glydrfreak/vSpeed-Vario/Documentation/TrackWheel.JPG

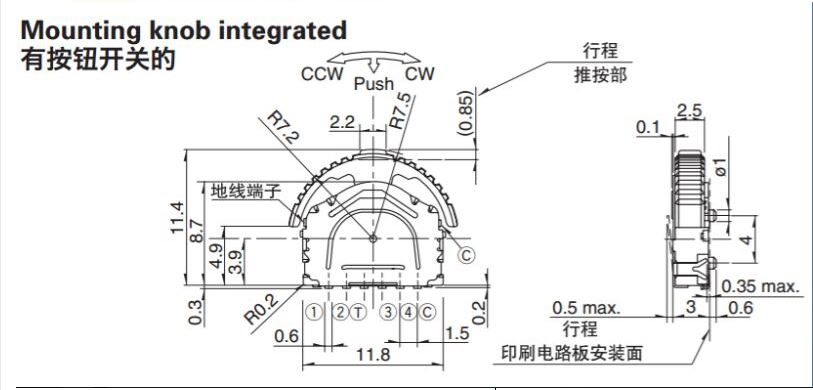
Documentation/TrackWheel.JPG
