glydrfreak/vSpeed-Vario/Documentation/vSpeed-mini-eBay/IMG-5799.JPG

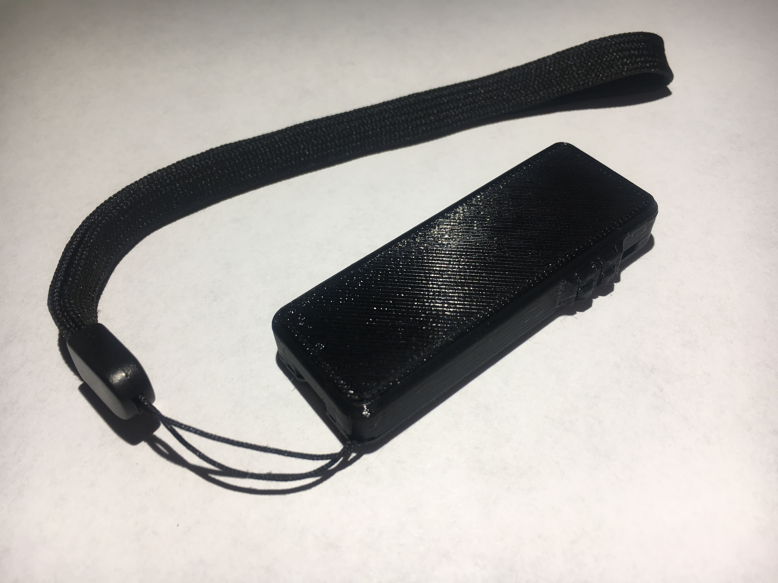
Documentation/vSpeed-mini-eBay/IMG-5799.JPG
