glydrfreak/vSpeed-Vario/Documentation/vSpeed-mini-eBay/IMG-5800.JPG

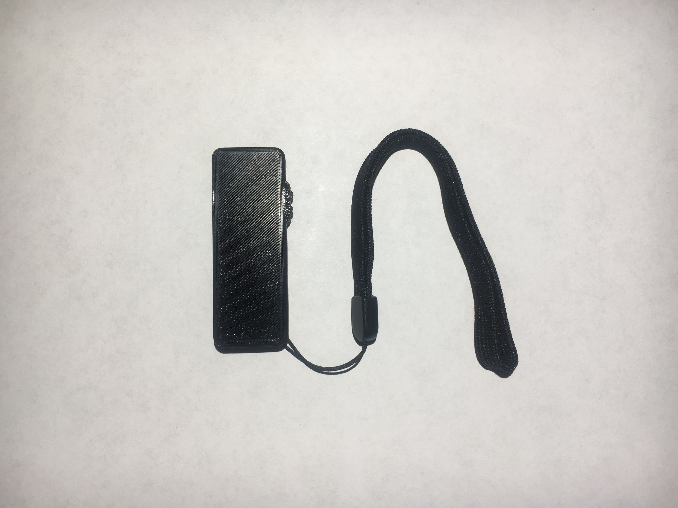
Documentation/vSpeed-mini-eBay/IMG-5800.JPG
