glydrfreak/vSpeed-Vario/Documentation/vSpeed-mini-eBay/IMG-5801.JPG

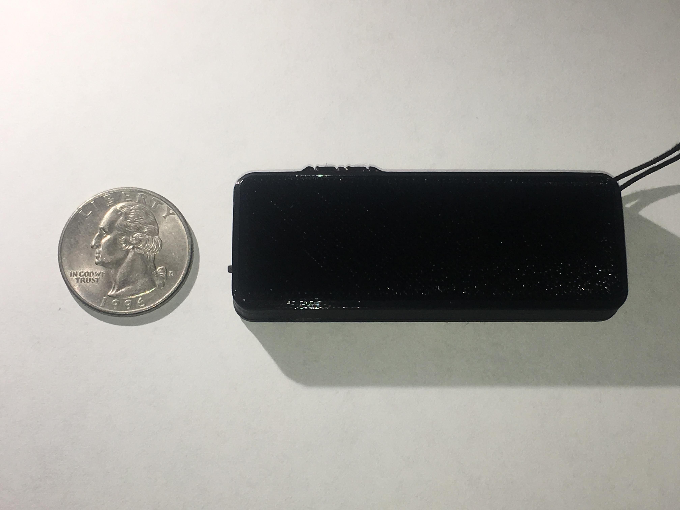
Documentation/vSpeed-mini-eBay/IMG-5801.JPG
