glydrfreak/vSpeed-Vario/Documentation/vSpeed-mini-eBay/IMG-5803.JPG

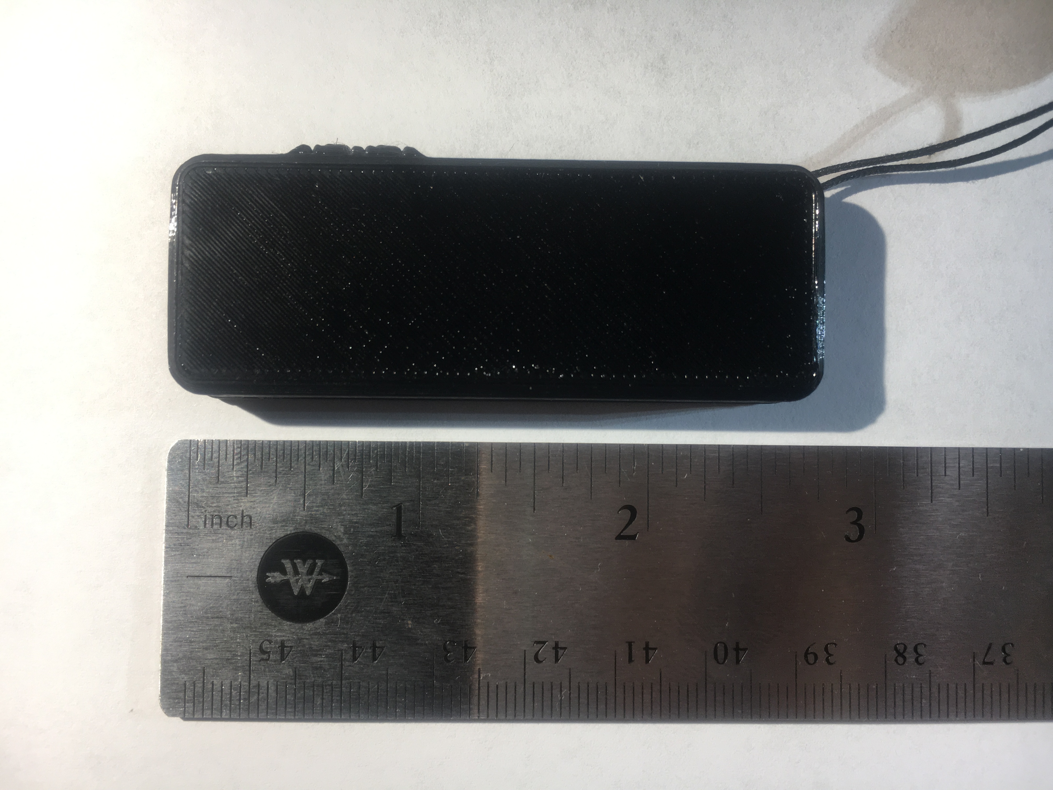
Documentation/vSpeed-mini-eBay/IMG-5803.JPG
