glydrfreak/vSpeed-Vario/Documentation/vSpeed-mini-eBay/IMG-5804.JPG

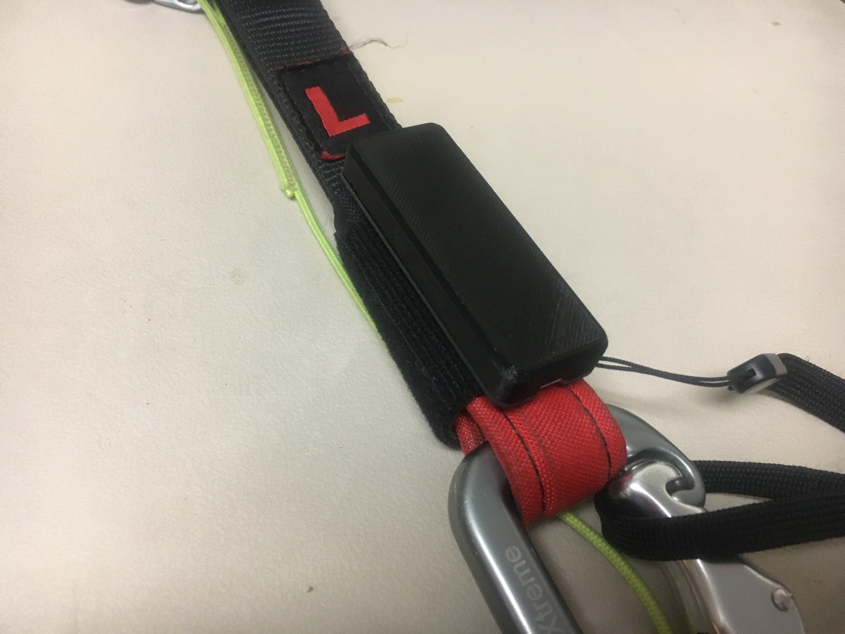
Documentation/vSpeed-mini-eBay/IMG-5804.JPG
