glydrfreak/vSpeed-Vario/Documentation/vSpeed-mini-eBay/IMG-5807.JPG

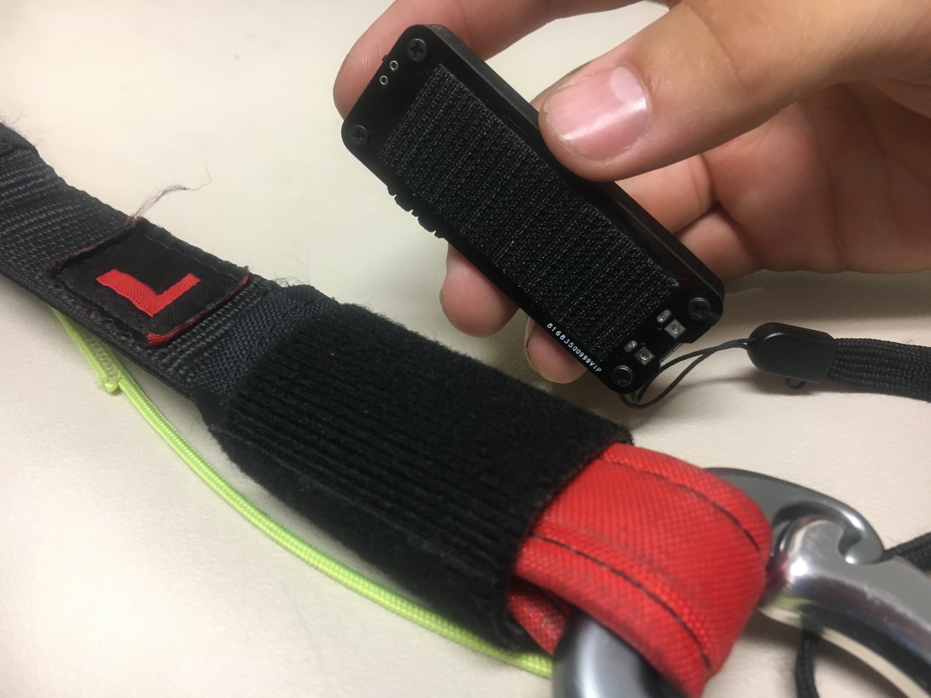
Documentation/vSpeed-mini-eBay/IMG-5807.JPG
