glydrfreak/vSpeed-Vario/Documentation/vSpeed-mini-eBay/IMG-5809.JPG

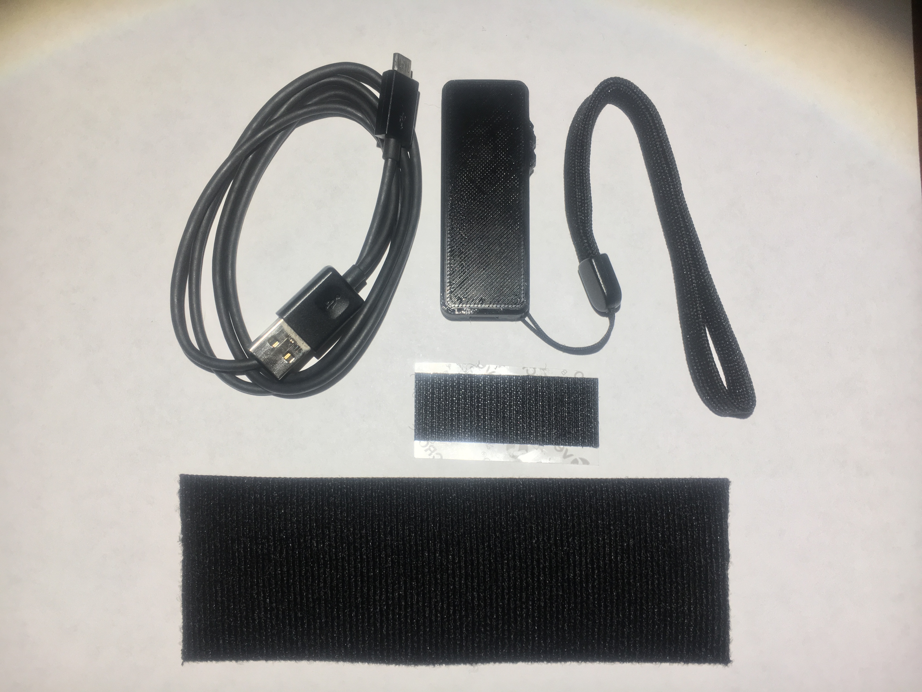
Documentation/vSpeed-mini-eBay/IMG-5809.JPG
