glydrfreak/vSpeed-Vario/Documentation/vSpeed-mini-eBay/IMG-6019.jpg

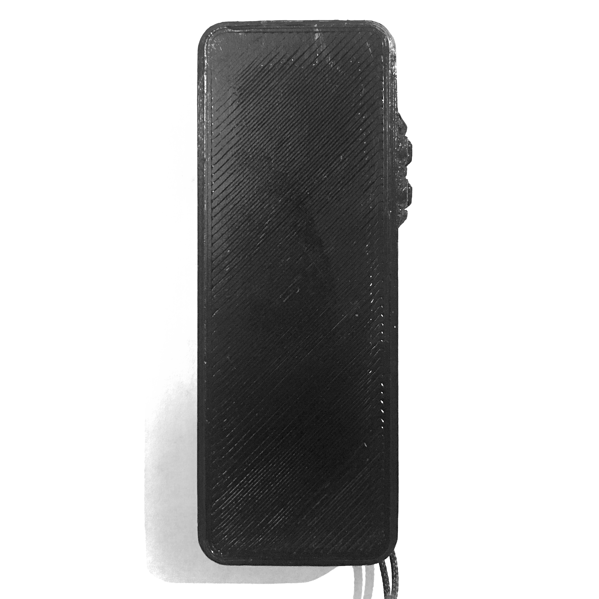
Documentation/vSpeed-mini-eBay/IMG-6019.jpg
