glydrfreak/vSpeed-Vario/Documentation/vSpeed-mini-eBay/vspeed_mini.jpg

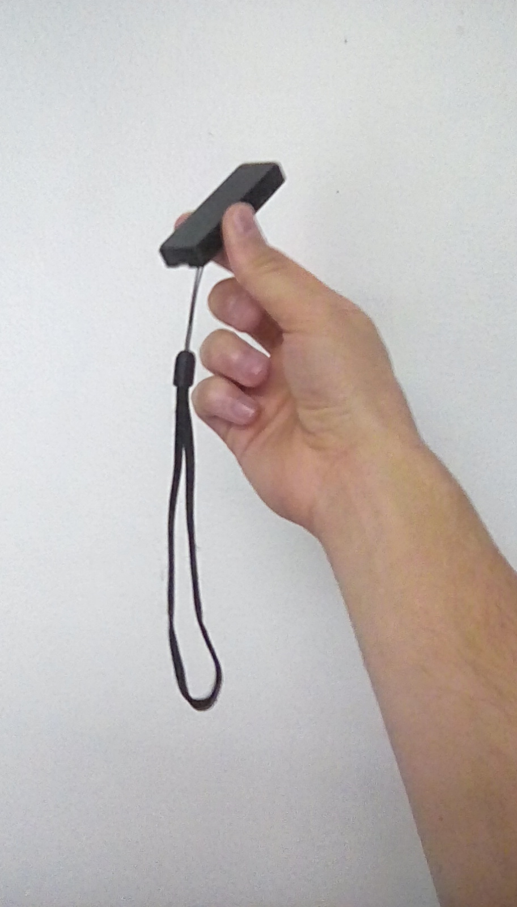
Documentation/vSpeed-mini-eBay/vspeed_mini.jpg
