glydrfreak/vSpeed-Vario/Documentation/vSpeed-mini-eBay/vSpeedMini3D - Copy.JPG

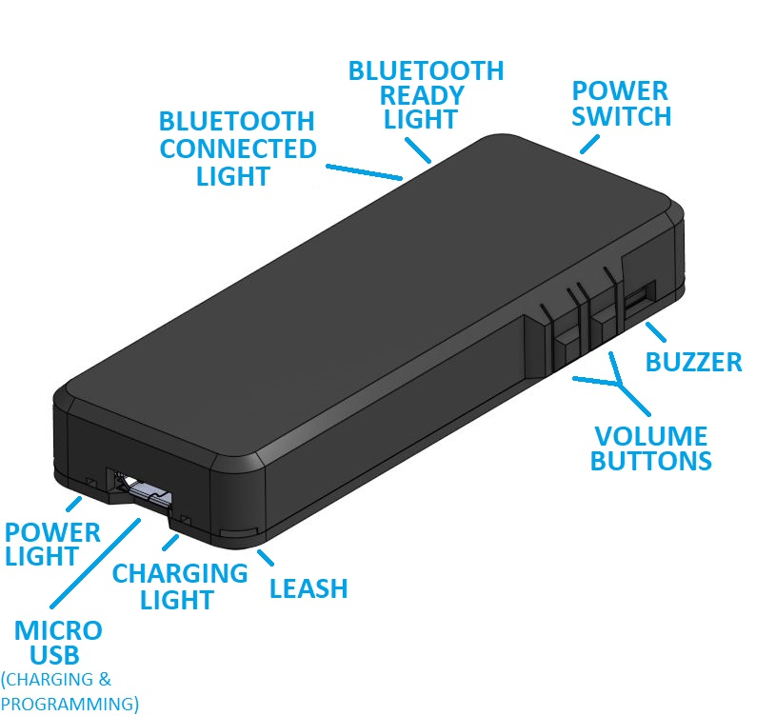
Documentation/vSpeed-mini-eBay/vSpeedMini3D - Copy.JPG
