glydrfreak/vSpeed-Vario/Images/COMPARE.JPG

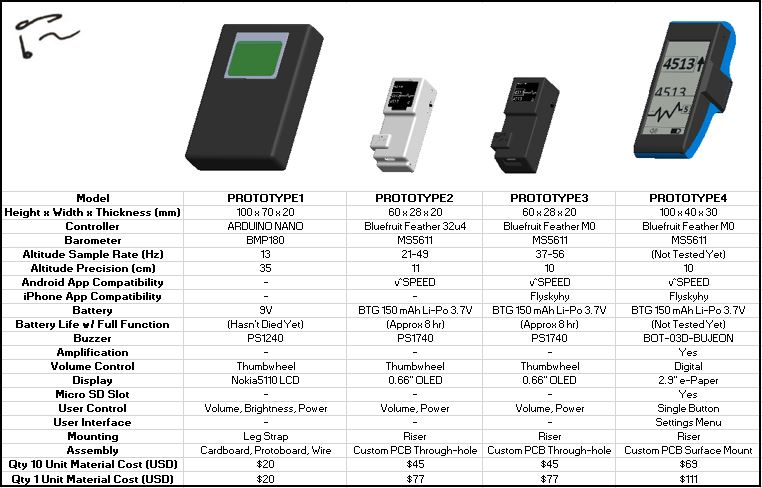
Images/COMPARE.JPG
