glydrfreak/vSpeed-Vario/Images/FAMILY.JPG

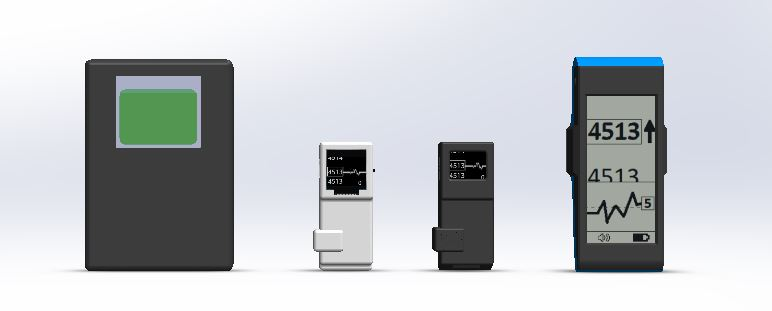
Images/FAMILY.JPG
