glydrfreak/vSpeed-Vario/Images/FAMILY_ISO.JPG

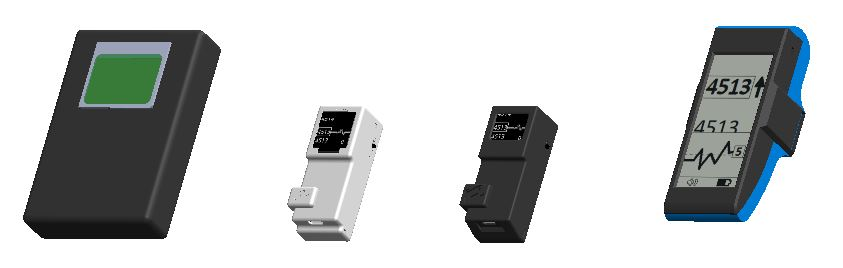
Images/FAMILY_ISO.JPG
