glydrfreak/vSpeed-Vario/Images/fsh.jpeg

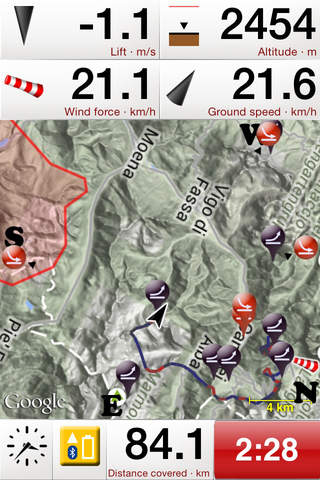
Images/fsh.jpeg
