glydrfreak/vSpeed-Vario/Images/labels.jpg

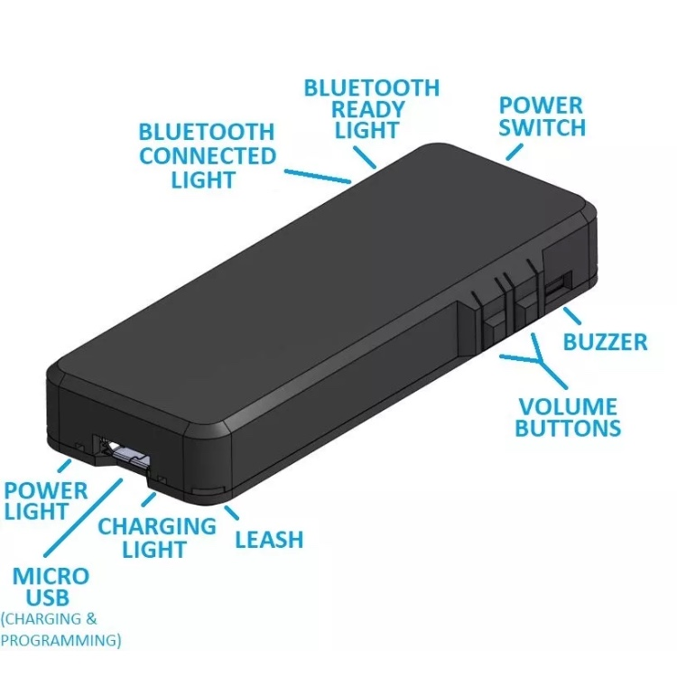
Images/labels.jpg
