glydrfreak/vSpeed-Vario/Images/NOKIA DISPLAY.png

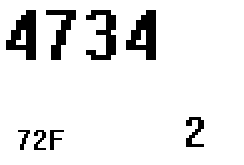
Images/NOKIA DISPLAY.png
