glydrfreak/vSpeed-Vario/Images/p4_preview.JPG

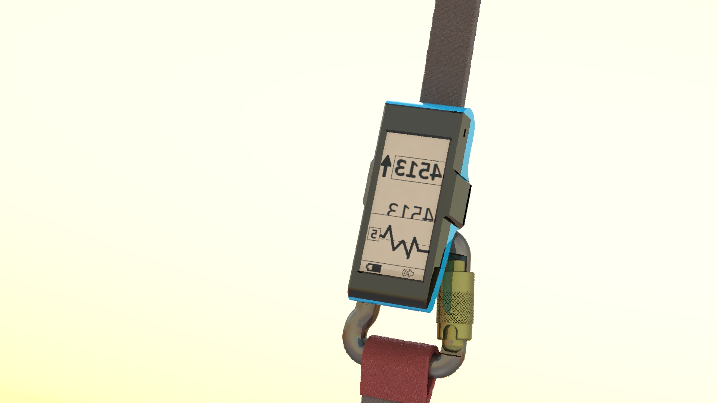
Images/p4_preview.JPG
