glydrfreak/vSpeed-Vario/Images/P5.JPG

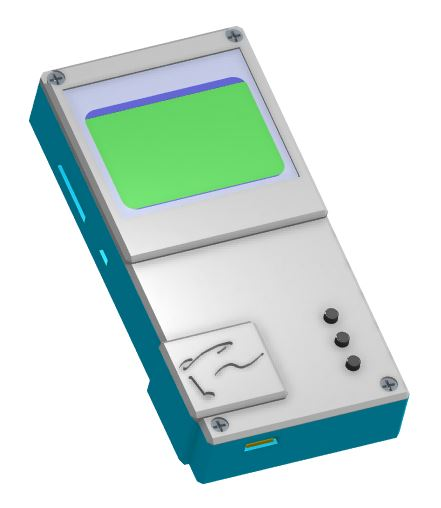
Images/P5.JPG
