glydrfreak/vSpeed-Vario/Images/P5_FOOTPRINT.JPG

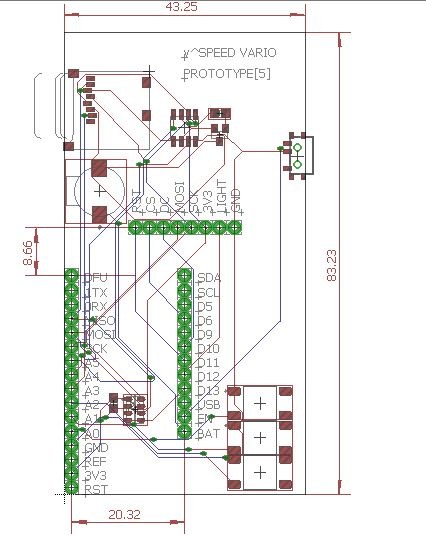
Images/P5_FOOTPRINT.JPG
