glydrfreak/vSpeed-Vario/Images/P5_PCB.JPG

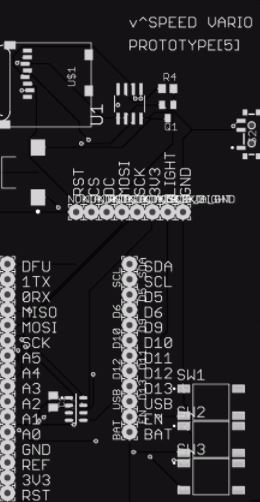
Images/P5_PCB.JPG
