glydrfreak/vSpeed-Vario/Images/P5_SIDE.JPG

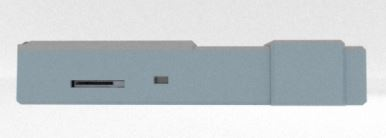
Images/P5_SIDE.JPG
