glydrfreak/vSpeed-Vario/Images/P5andP6.JPG

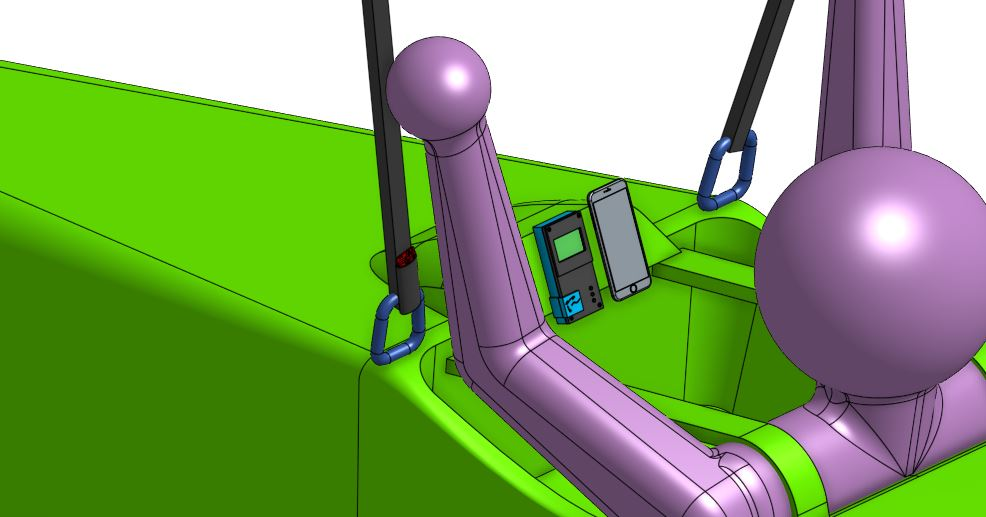
Images/P5andP6.JPG
