glydrfreak/vSpeed-Vario/Images/P6_PCB.JPG

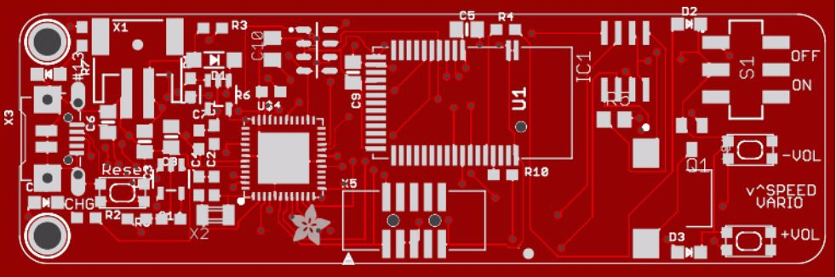
Images/P6_PCB.JPG
