glydrfreak/vSpeed-Vario/Images/P6_PCB_V2.JPG

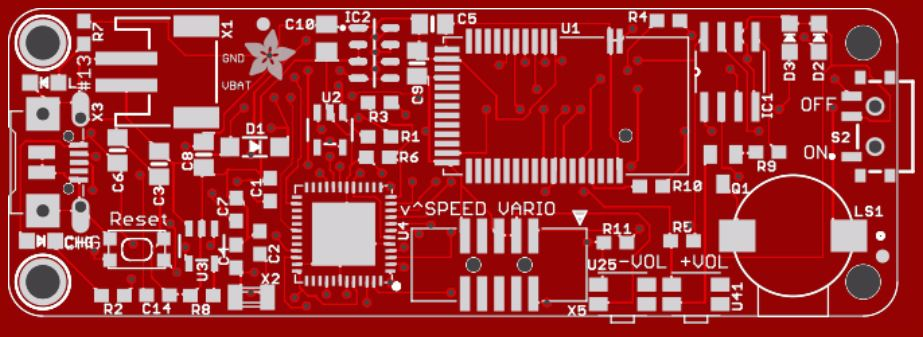
Images/P6_PCB_V2.JPG
