glydrfreak/vSpeed-Vario/Images/P6_PCB_V3.JPG

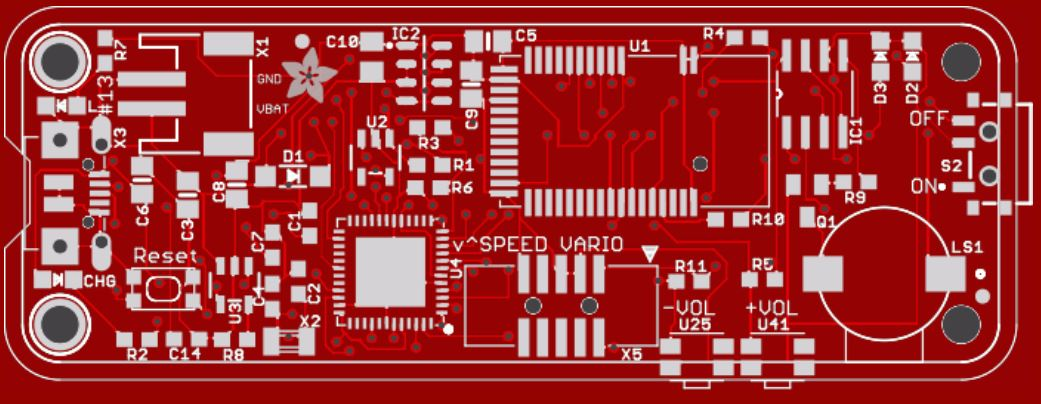
Images/P6_PCB_V3.JPG
