glydrfreak/vSpeed-Vario/Images/PROTOTYPE2.jpg

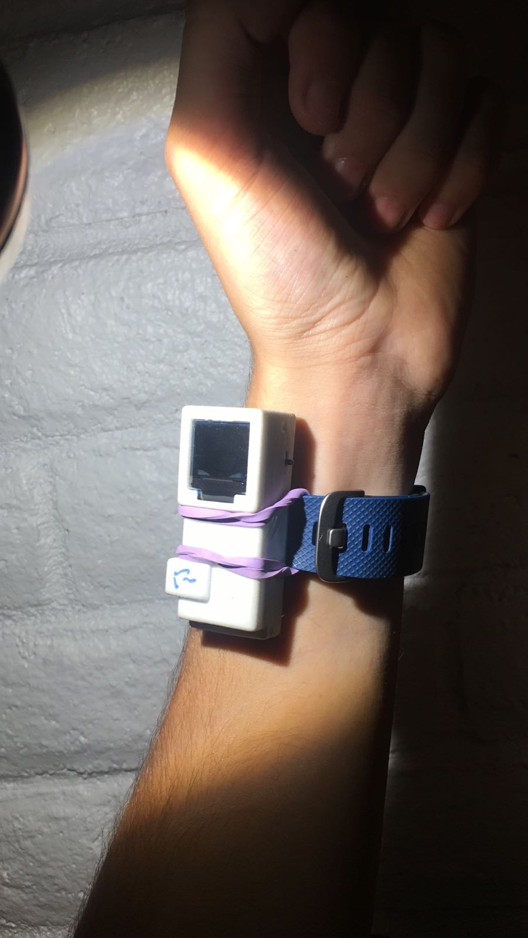
Images/PROTOTYPE2.jpg
