glydrfreak/vSpeed-Vario/Images/PROTOTYPE3AND4.JPG

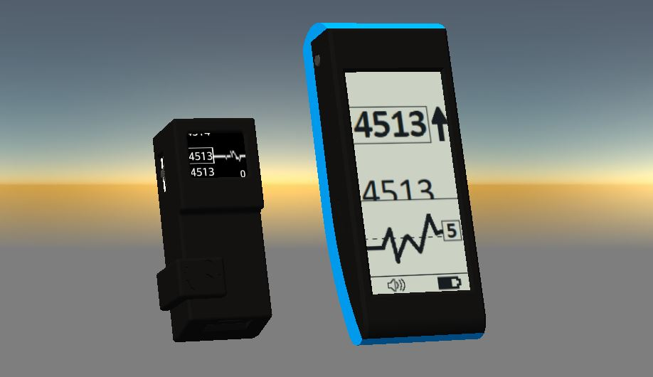
Images/PROTOTYPE3AND4.JPG
