glydrfreak/vSpeed-Vario/Images/PROTOTYPE3uncropped.jpg

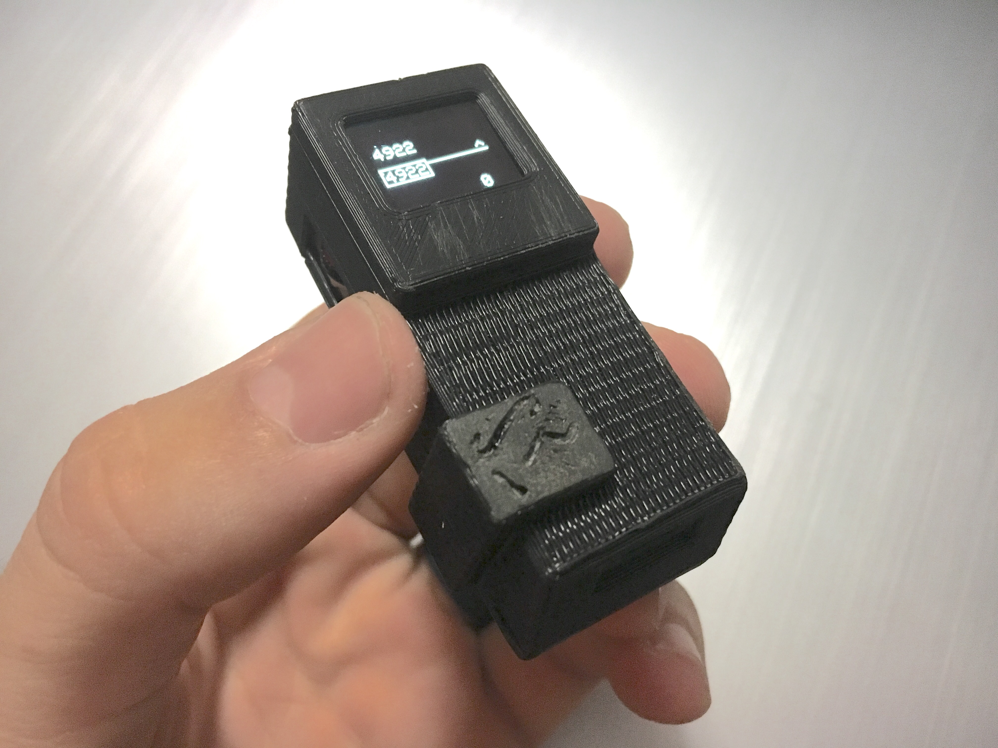
Images/PROTOTYPE3uncropped.jpg
