glydrfreak/vSpeed-Vario/Images/PROTOTYPE4.jpg

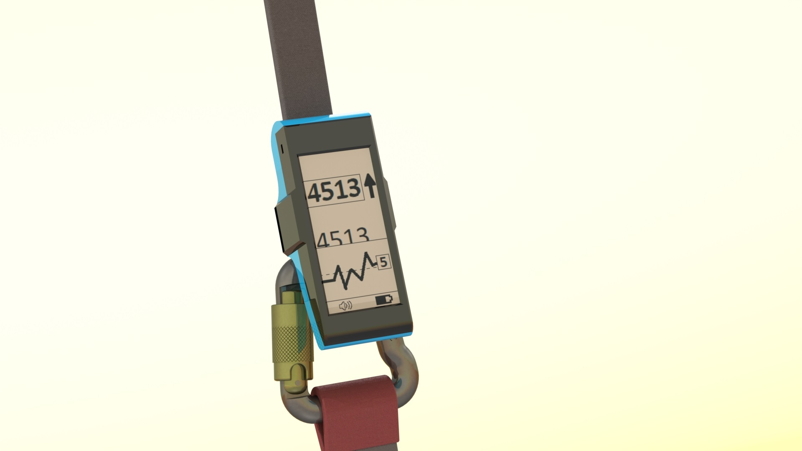
Images/PROTOTYPE4.jpg
