glydrfreak/vSpeed-Vario/Images/REFLOW_TOASTER_PCB.JPG

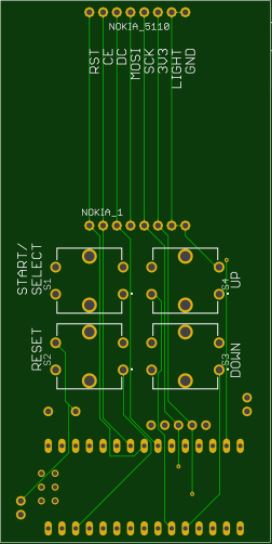
Images/REFLOW_TOASTER_PCB.JPG
