glydrfreak/vSpeed-Vario/Images/ssf3.JPG

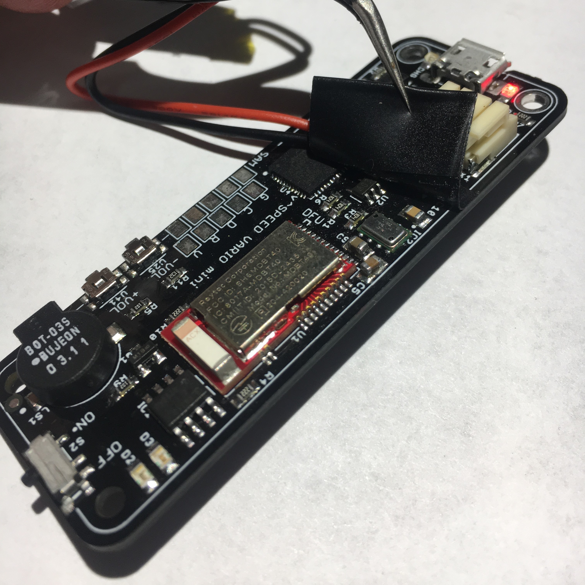
Images/ssf3.JPG
