glydrfreak/vSpeed-Vario/Images/ssf4.JPG

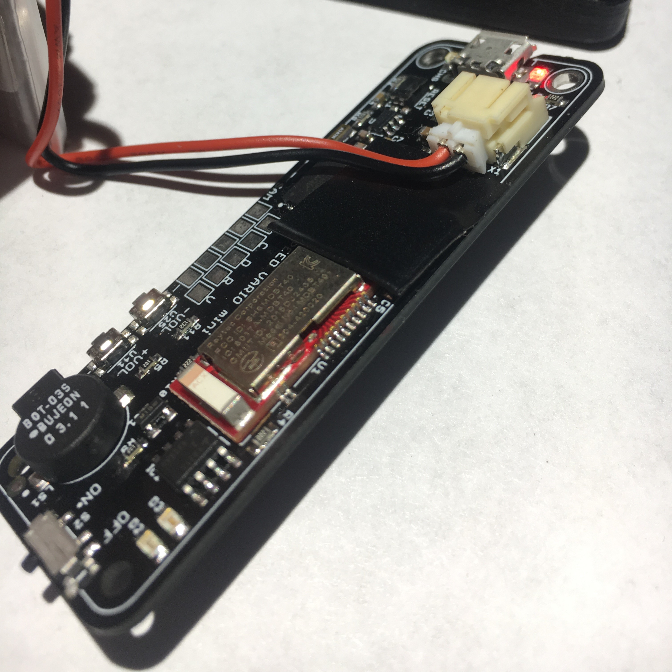
Images/ssf4.JPG
