glydrfreak/vSpeed-Vario/SolidWorks/P1.new/frente.jpg

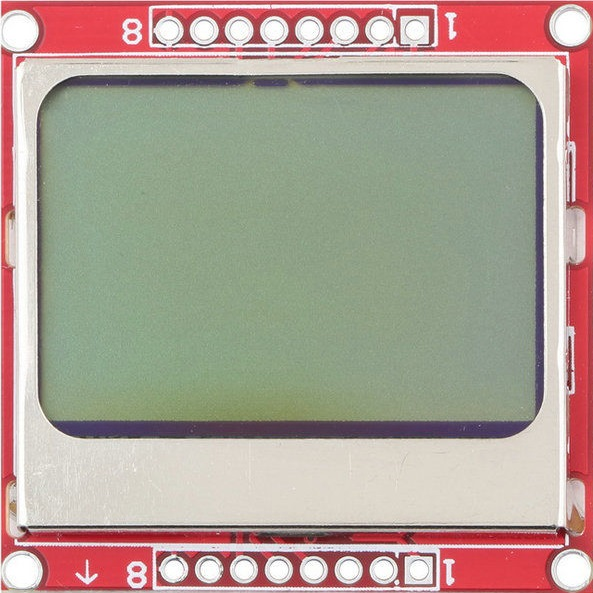
SolidWorks/P1.new/frente.jpg
