glydrfreak/vSpeed-Vario/SolidWorks/P1.new/tras.jpg

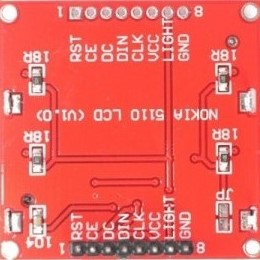
SolidWorks/P1.new/tras.jpg
