glydrfreak/vSpeed-Vario/SolidWorks/P2.new/android.jpg

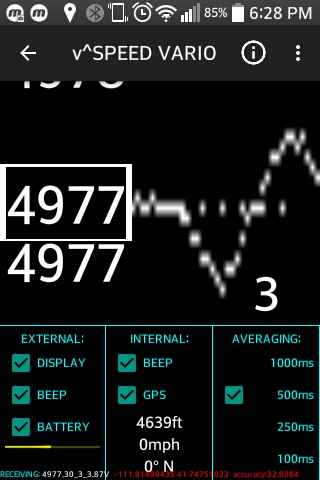
SolidWorks/P2.new/android.jpg
