glydrfreak/vSpeed-Vario/SolidWorks/P2.new/bluefruit feather 32u4 bottom.jpg

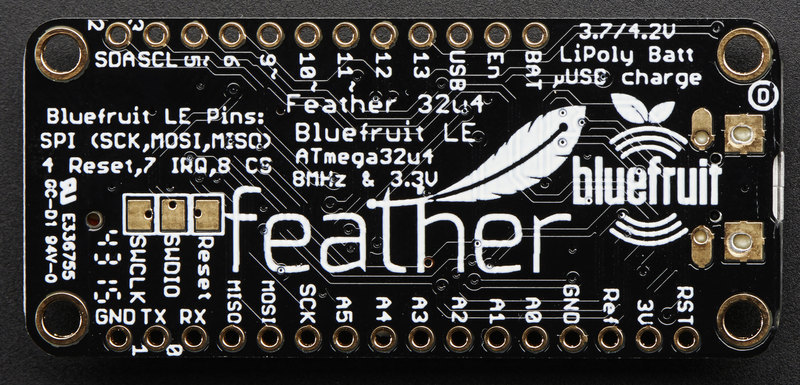
SolidWorks/P2.new/bluefruit feather 32u4 bottom.jpg
