glydrfreak/vSpeed-Vario/SolidWorks/P2.new/bluefruit feather 32u4.jpg

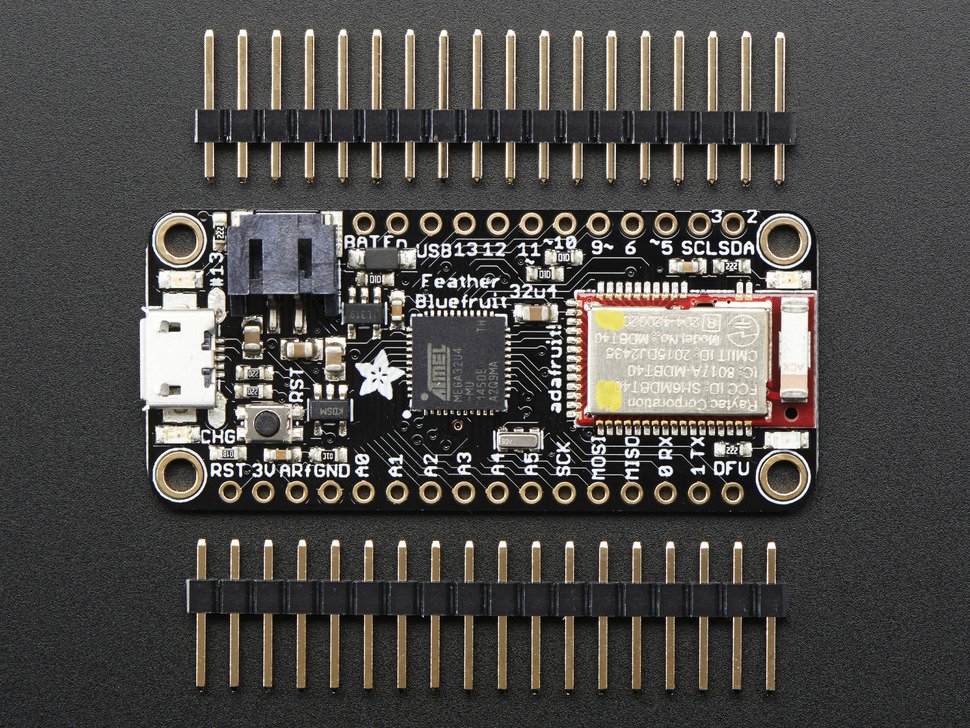
SolidWorks/P2.new/bluefruit feather 32u4.jpg
