glydrfreak/vSpeed-Vario/SolidWorks/P2.new/custom pcb 1.2.4.jpg

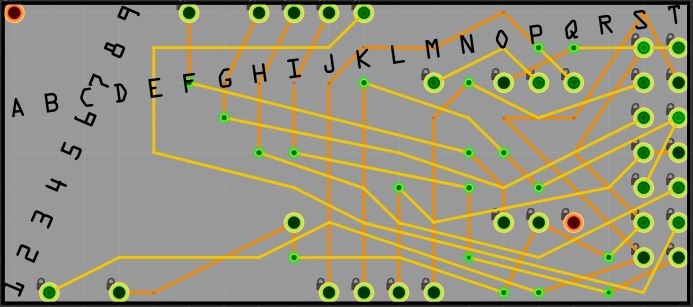
SolidWorks/P2.new/custom pcb 1.2.4.jpg
