glydrfreak/vSpeed-Vario/SolidWorks/P2.new/ms5611.jpg

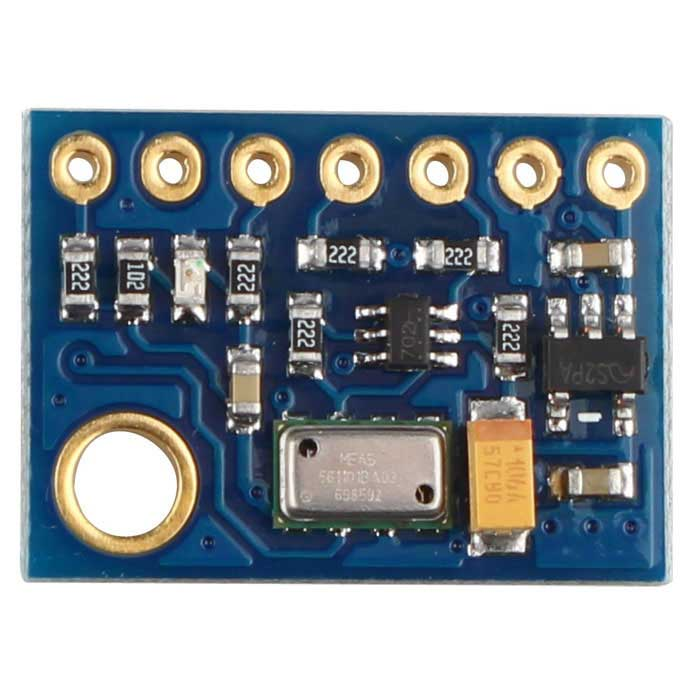
SolidWorks/P2.new/ms5611.jpg
