glydrfreak/vSpeed-Vario/SolidWorks/P2.new/s-l1600 (1).jpg

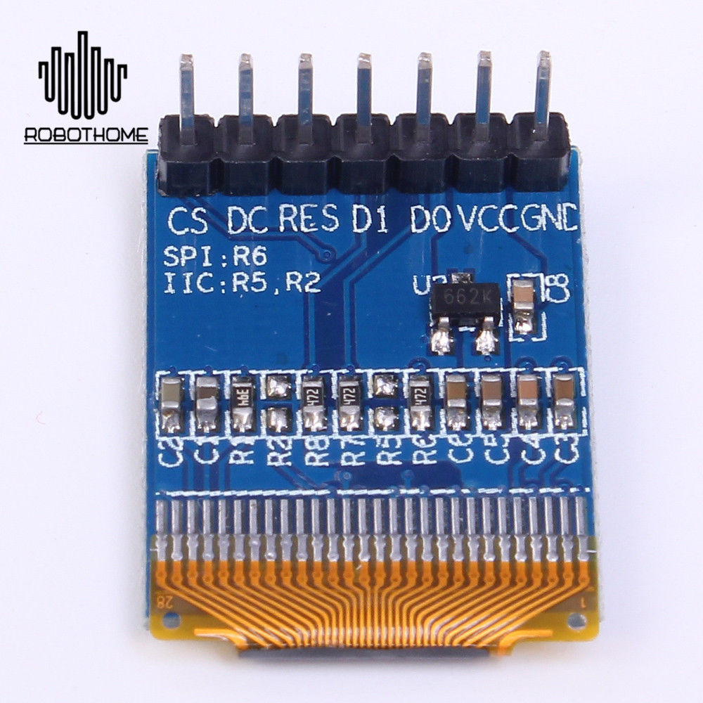
SolidWorks/P2.new/s-l1600 (1).jpg
