glydrfreak/vSpeed-Vario/SolidWorks/P4.new/bottom_pcb.jpg

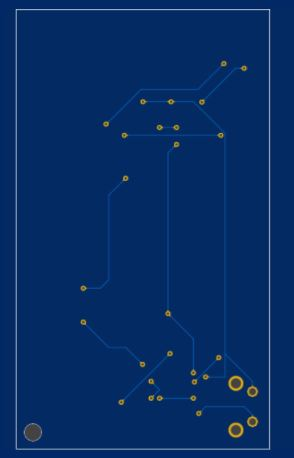
SolidWorks/P4.new/bottom_pcb.jpg
