glydrfreak/vSpeed-Vario/SolidWorks/P4.new/cotton burgundy.jpg

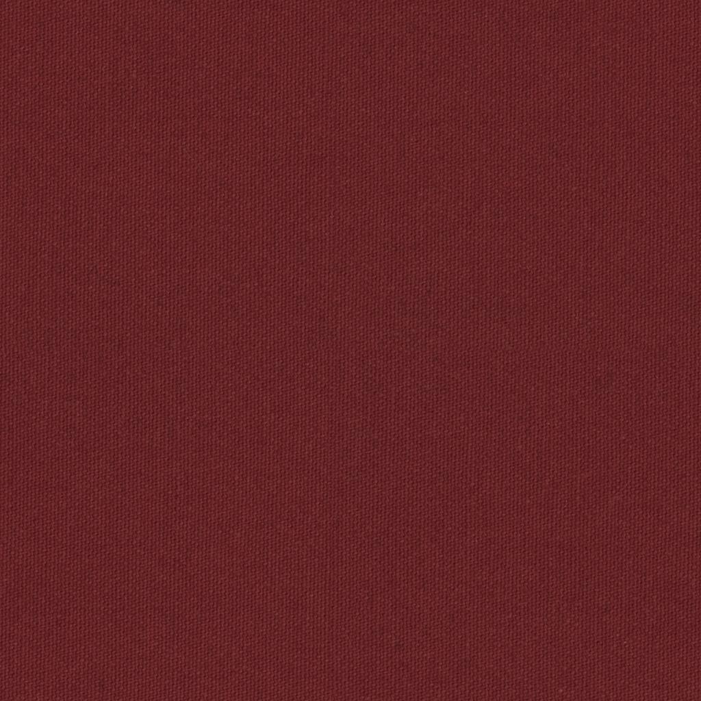
SolidWorks/P4.new/cotton burgundy.jpg
