glydrfreak/vSpeed-Vario/SolidWorks/P4.new/cotton grey.jpg

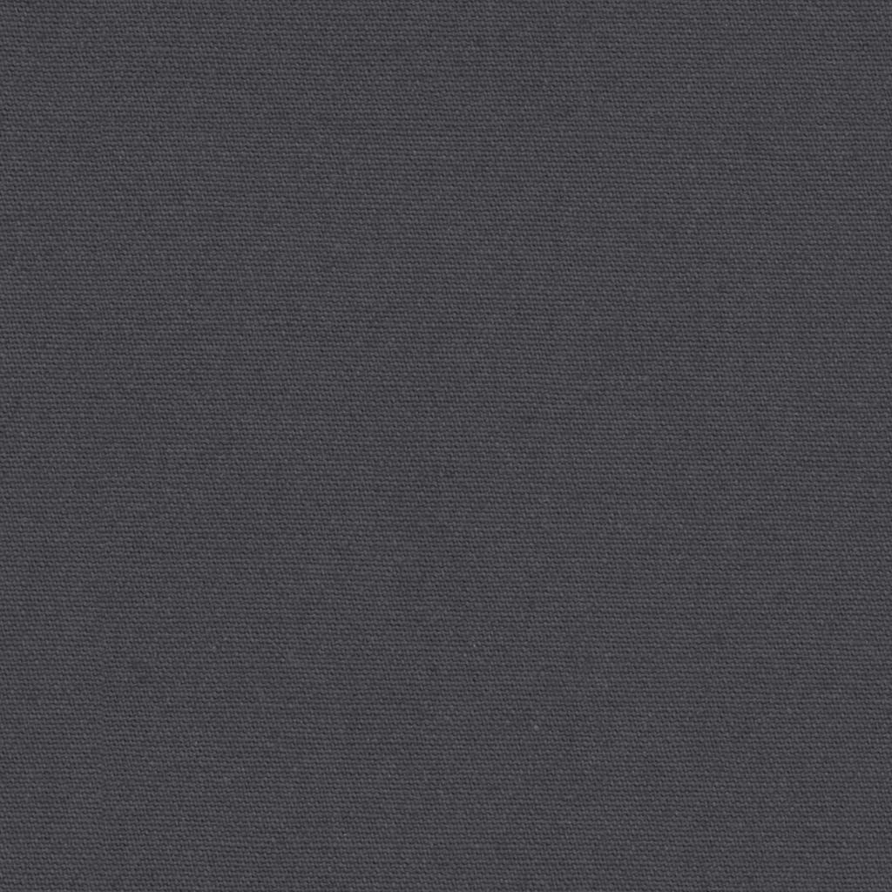
SolidWorks/P4.new/cotton grey.jpg
