glydrfreak/vSpeed-Vario/SolidWorks/P4.new/sky_environment.jpg

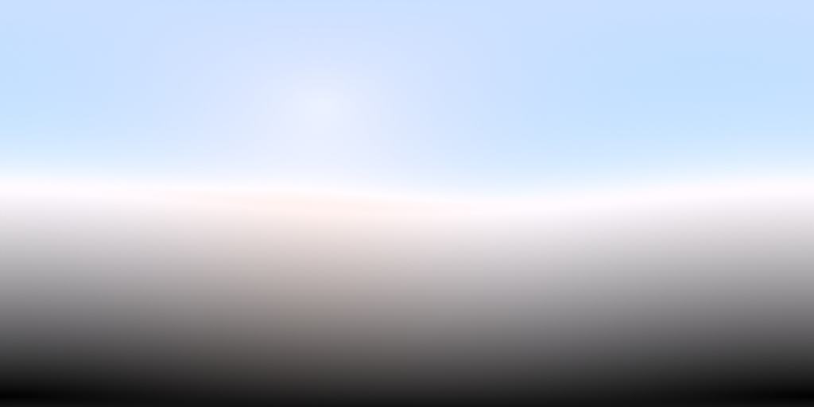
SolidWorks/P4.new/sky_environment.jpg
