glydrfreak/vSpeed-Vario/SolidWorks/P4/COMPARISON.JPG

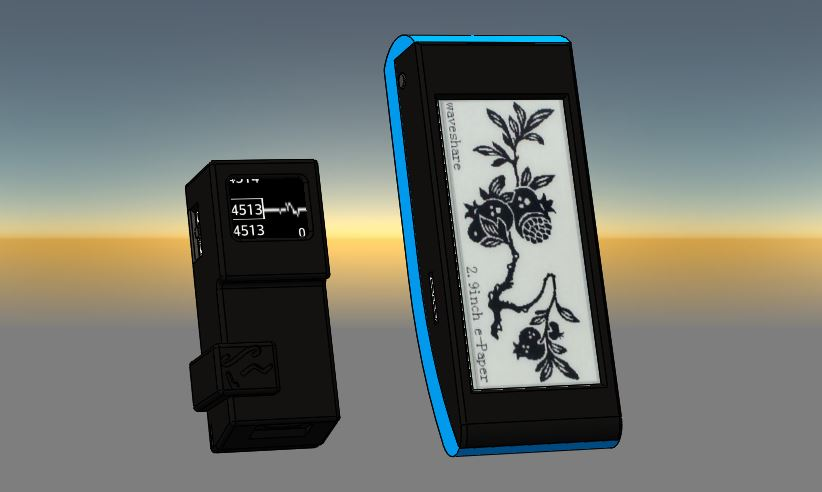
SolidWorks/P4/COMPARISON.JPG
