glydrfreak/vSpeed-Vario/SolidWorks/P4/PLACEMENT.JPG

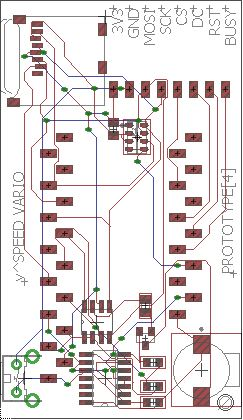
SolidWorks/P4/PLACEMENT.JPG
