glydrfreak/vSpeed-Vario/SolidWorks/P4/ROUGH ACTUAL SIZE.JPG

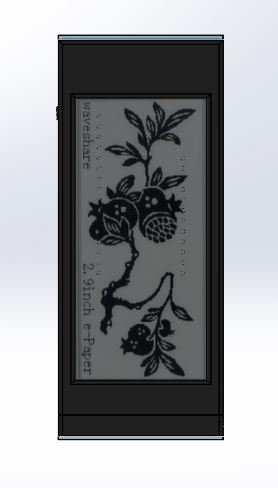
SolidWorks/P4/ROUGH ACTUAL SIZE.JPG
