glydrfreak/vSpeed-Vario/SolidWorks/P4/SCREEN_COMPARISON.JPG

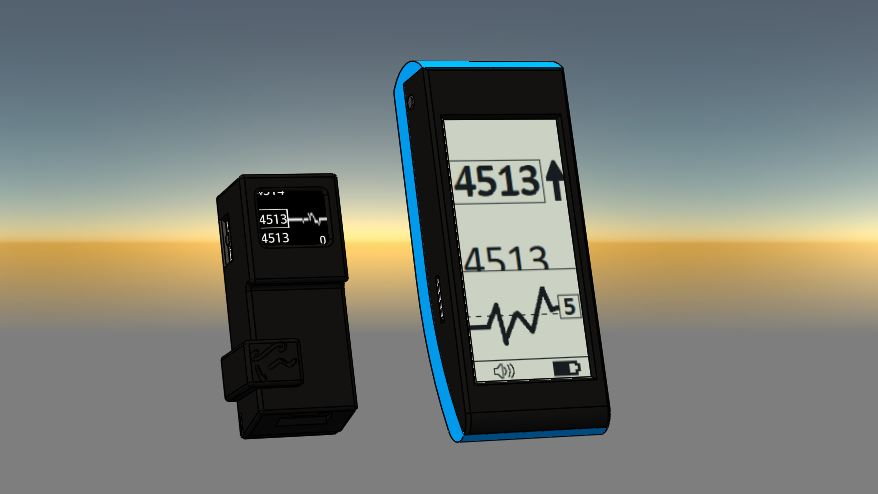
SolidWorks/P4/SCREEN_COMPARISON.JPG
