glydrfreak/vSpeed-Vario/SolidWorks/P4/stencil.JPG

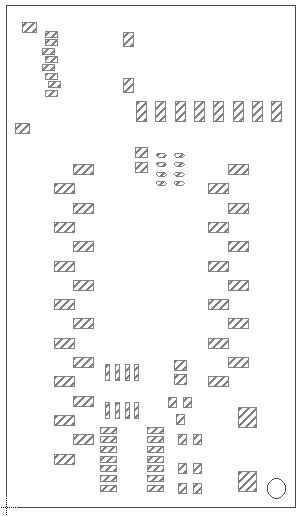
SolidWorks/P4/stencil.JPG
