glydrfreak/vSpeed-Vario/SolidWorks/P4/sunset.JPG

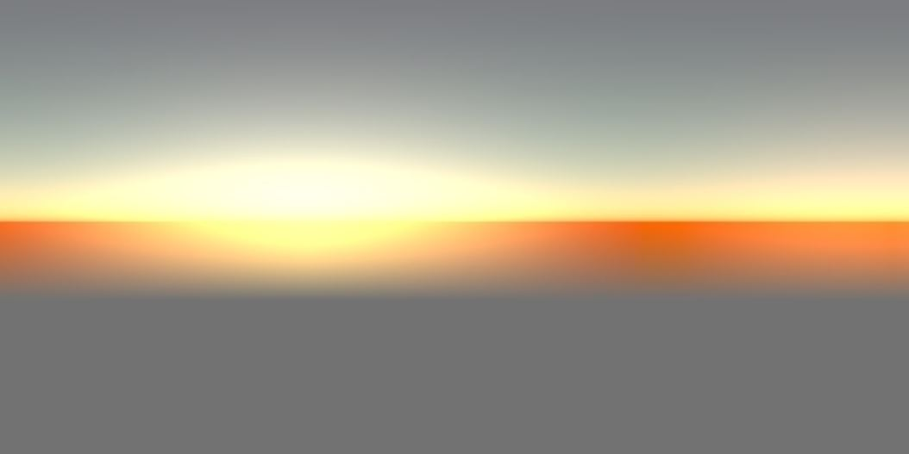
SolidWorks/P4/sunset.JPG
