glydrfreak/vSpeed-Vario/SolidWorks/P6/BOM_Template_2017_06_30.csv

Designator | Manufacturer Part Number | Quantity
C1,C2,C3,C4,C5 | RHA0J471MCN1GS | 5
A1,A4 | 318020010 | 2
D1 | CYBLE-014008-00 | 1
