glydrfreak/vSpeed-Vario/BillOfMaterials/ExplodedView.JPG

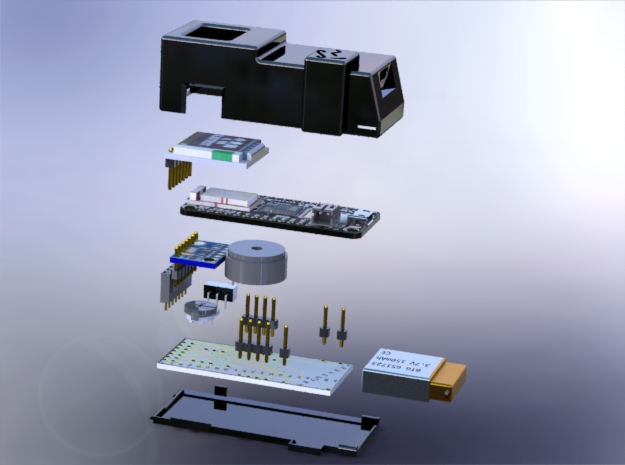
BillOfMaterials/ExplodedView.JPG
