glydrfreak/vSpeed-Vario/SolidWorks/P5/V2/CASE_FRONT V2.stl

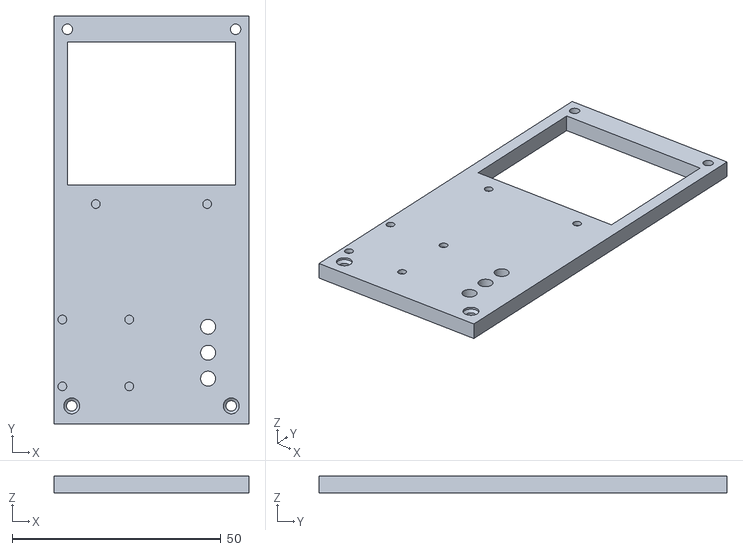
[picture p93: CAD file, 2018-03-19]
SolidWorks/P5/V2/CASE_FRONT V2.stl
46.7 x 97.6 x 4.00
