glydrfreak/vSpeed-Vario/SolidWorks/P6/3220-10-0300/3220-10-0300.igs

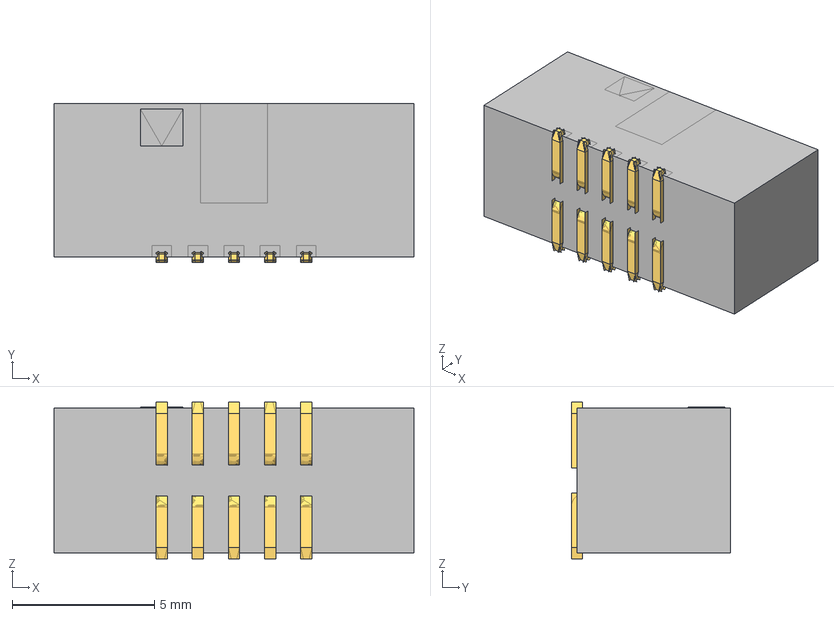
[picture p94: CAD file, 2018-04-02]
SolidWorks/P6/3220-10-0300/3220-10-0300.igs
12.7 x 5.60 x 5.50 mm
