glydrfreak/vSpeed-Vario/SolidWorks/P6/P6_CASE.stl

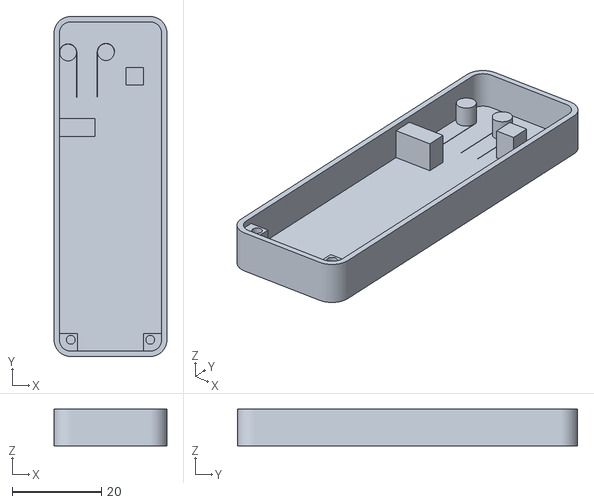
[picture p95: CAD file, 2018-04-02]
SolidWorks/P6/P6_CASE.stl
25.3 x 76.1 x 8.20
