glydrfreak/vSpeed-Vario/SolidWorks/P1.new/placa.SLDPRT

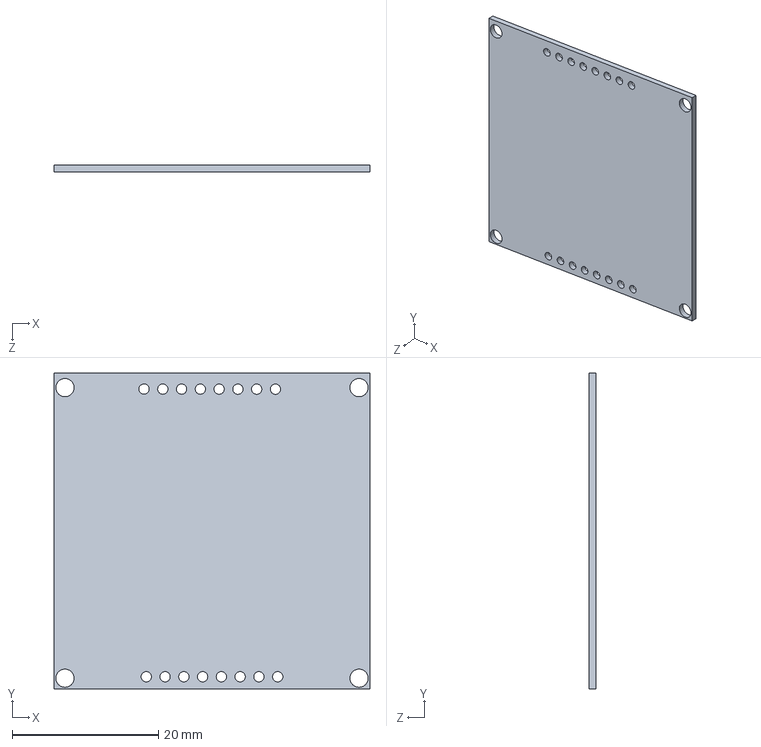
[picture p96: CAD file, 2017-11-29]
SolidWorks/P1.new/placa.SLDPRT
43.2 x 43.2 x 1.00 mm
