glydrfreak/vSpeed-Vario/SolidWorks/P2.new/POT THUMBWHEEL HORIZONTAL.SLDPRT

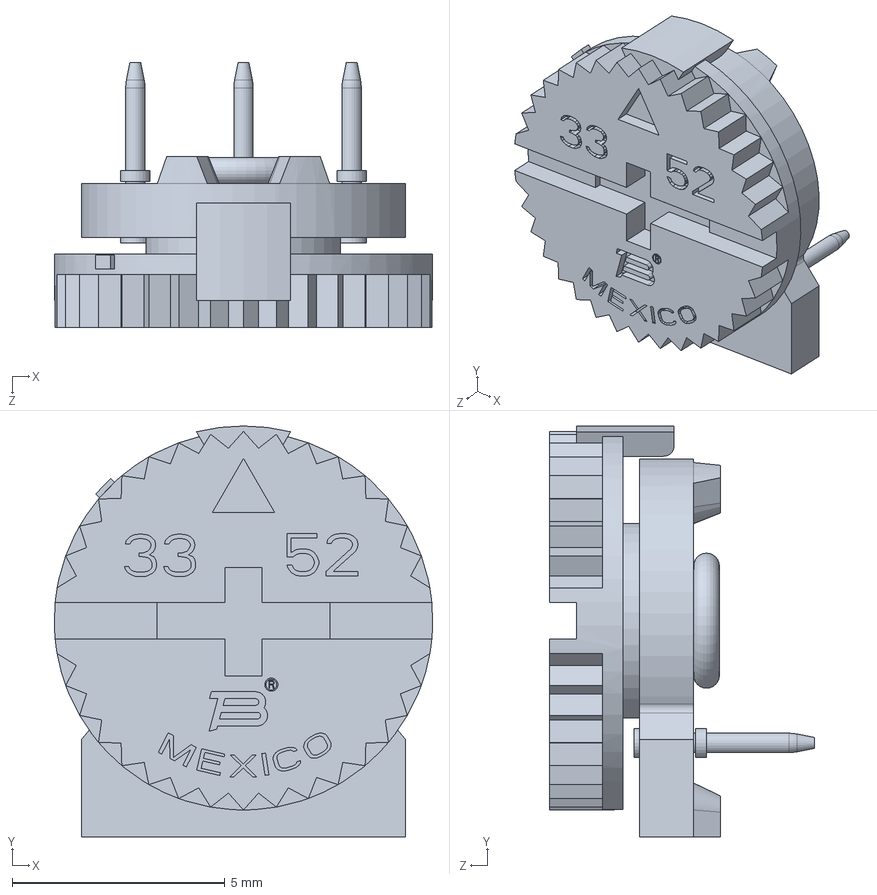
[picture p97: CAD file, 2017-11-29]
SolidWorks/P2.new/POT THUMBWHEEL HORIZONTAL.SLDPRT
8.89 x 9.65 x 6.22 mm
