glydrfreak/vSpeed-Vario/SolidWorks/P4.new/P4_BLUEFRUIT FEATHER.SLDPRT

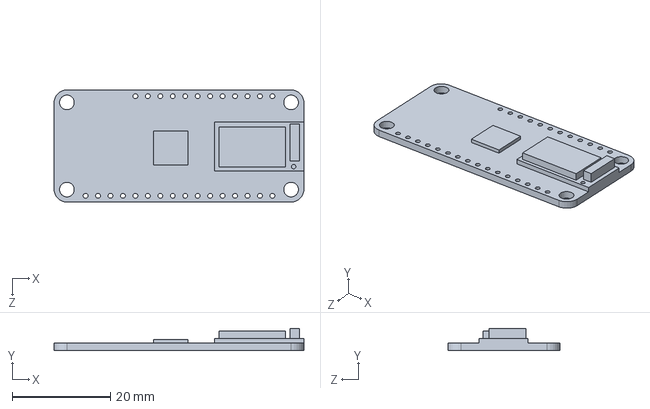
[picture p98: CAD file, 2018-03-09]
SolidWorks/P4.new/P4_BLUEFRUIT FEATHER.SLDPRT
51.0 x 4.50 x 22.9 mm
