glydrfreak/vSpeed-Vario/SolidWorks/P4/P4_JST XH 8 S8B-XH-A1 shrouded header connector v4.SLDPRT

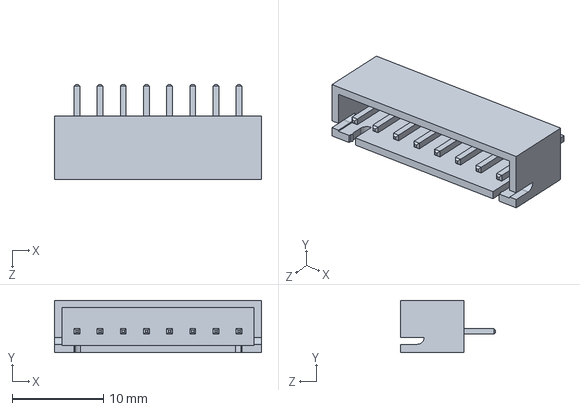
[picture p99: CAD file, 2017-12-11]
SolidWorks/P4/P4_JST XH 8 S8B-XH-A1 shrouded header connector v4.SLDPRT
22.7 x 5.75 x 10.4 mm
