glydrfreak/vSpeed-Vario/SolidWorks/P5/V2/CASE_CORNER V2.stl

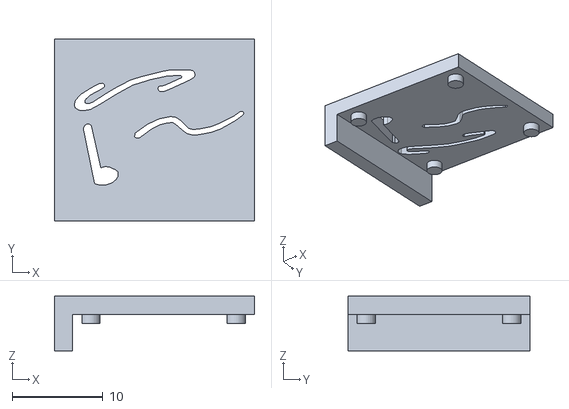
[picture p100: CAD file, 2018-03-19]
SolidWorks/P5/V2/CASE_CORNER V2.stl
22.0 x 20.0 x 6.00
