glydrfreak/vSpeed-Vario/SolidWorks/P6/XZxx54-1.sldprt

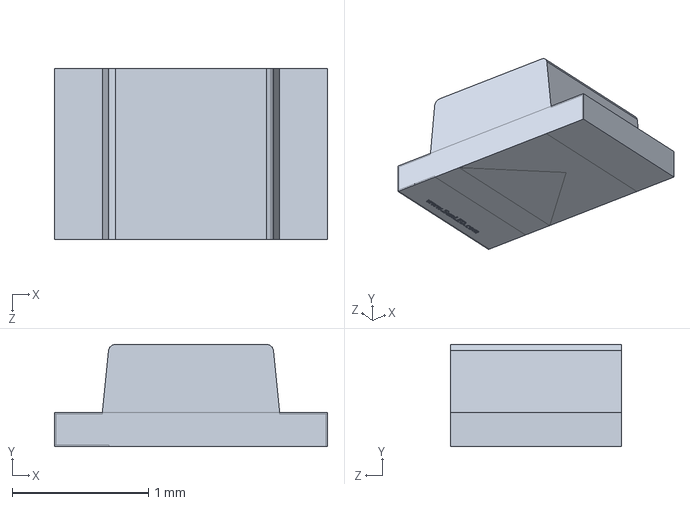
[picture p101: CAD file, 2018-04-02]
SolidWorks/P6/XZxx54-1.sldprt
2.00 x 0.75 x 1.25 mm
