glydrfreak/vSpeed-Vario/SolidWorks/P2.new/P2 CASE - FRONT SHELL.SLDPRT

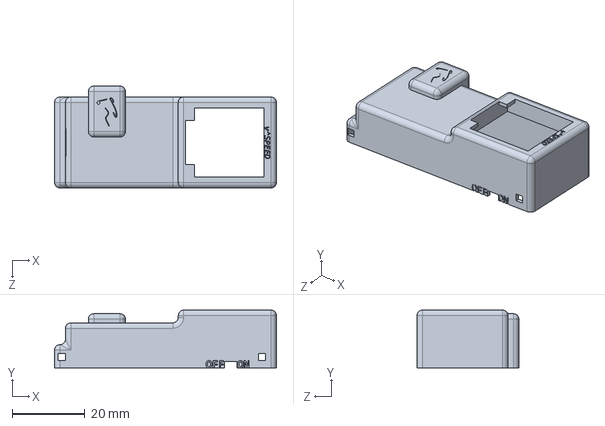
[picture p102: CAD file, 2017-11-29]
SolidWorks/P2.new/P2 CASE - FRONT SHELL.SLDPRT
61.0 x 15.9 x 28.0 mm
