glydrfreak/vSpeed-Vario/SolidWorks/P3.new/p3_PS1740.SLDPRT

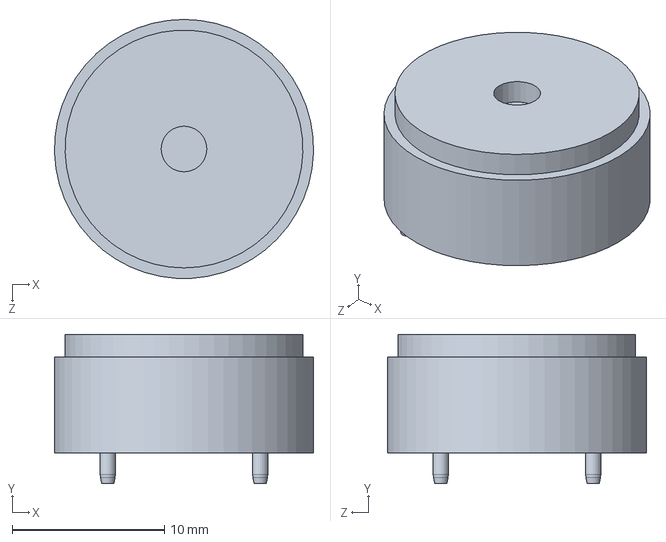
[picture p103: CAD file, 2017-11-29]
SolidWorks/P3.new/p3_PS1740.SLDPRT
17.0 x 9.80 x 17.0 mm
