glydrfreak/vSpeed-Vario/SolidWorks/P4/P4_PCB_FOR_2.9_EPD.SLDPRT

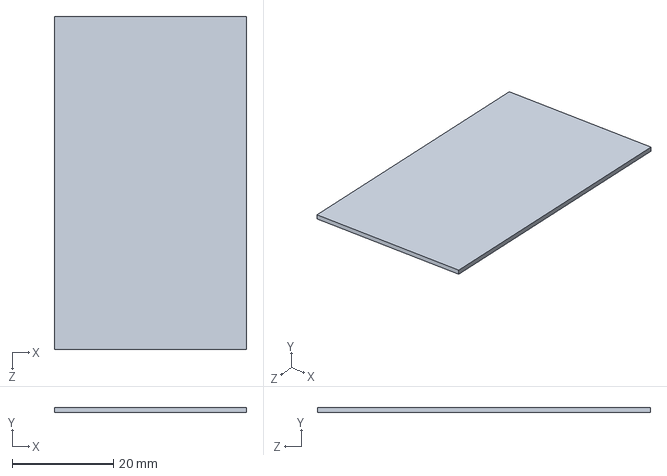
[picture p104: CAD file, 2017-12-11]
SolidWorks/P4/P4_PCB_FOR_2.9_EPD.SLDPRT
38.0 x 1.00 x 66.0 mm
