glydrfreak/vSpeed-Vario/SolidWorks/P5/V2/CASE_TRIM V2.stl

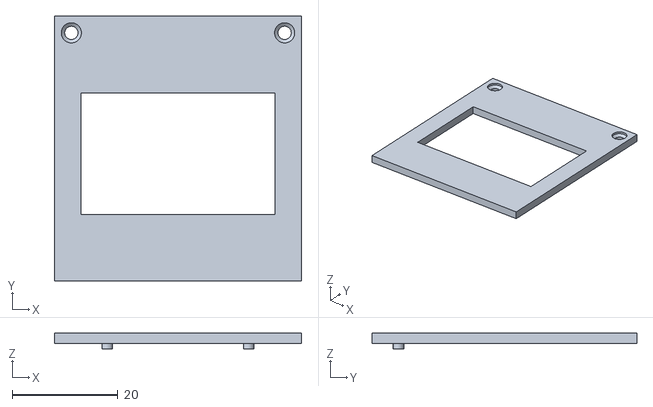
[picture p105: CAD file, 2018-03-19]
SolidWorks/P5/V2/CASE_TRIM V2.stl
46.7 x 50.0 x 3.00
