glydrfreak/vSpeed-Vario/SolidWorks/P1.new/cristal_liquido.SLDPRT

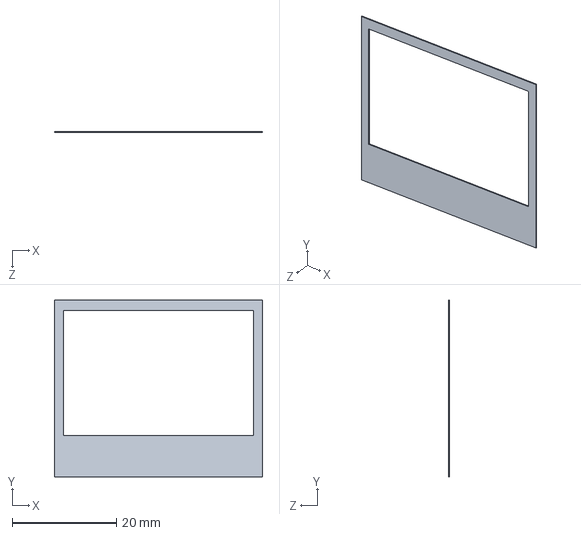
[picture p106: CAD file, 2017-11-29]
SolidWorks/P1.new/cristal_liquido.SLDPRT
40.0 x 34.0 x 0.2 mm
