glydrfreak/vSpeed-Vario/SolidWorks/P2.new/JST 2pin rightangle.SLDPRT

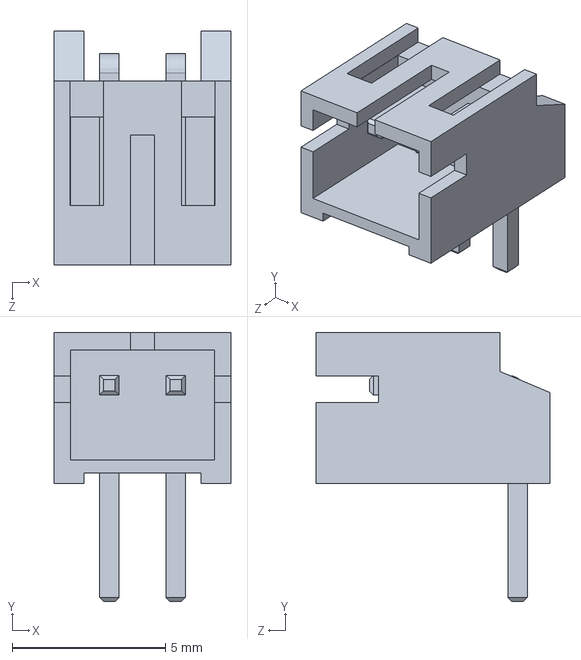
[picture p107: CAD file, 2017-11-29]
SolidWorks/P2.new/JST 2pin rightangle.SLDPRT
5.77 x 8.76 x 7.62 mm
