glydrfreak/vSpeed-Vario/SolidWorks/P3.new/p3_BTG 3.7V 150mAh LIPO.SLDPRT

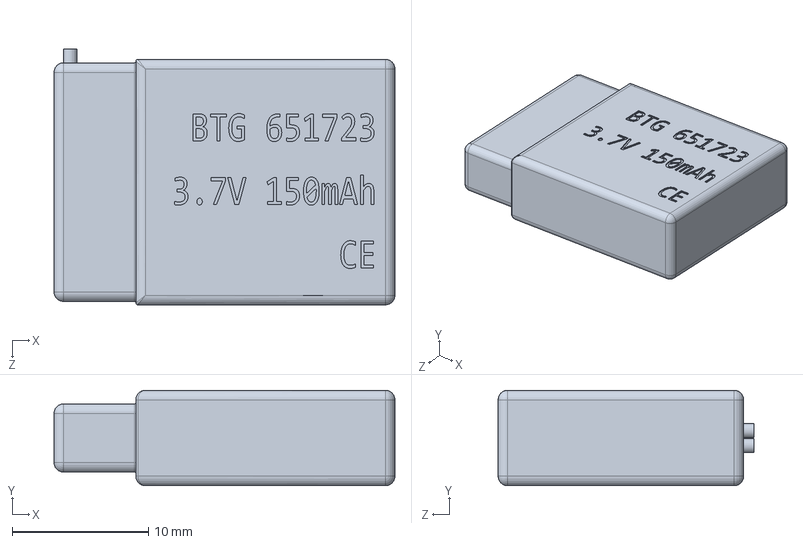
[picture p108: CAD file, 2017-11-29]
SolidWorks/P3.new/p3_BTG 3.7V 150mAh LIPO.SLDPRT
25.0 x 7.00 x 18.8 mm
