glydrfreak/vSpeed-Vario/SolidWorks/P4.new/P4_BOT-03D PASSIVE BUZZER.SLDPRT

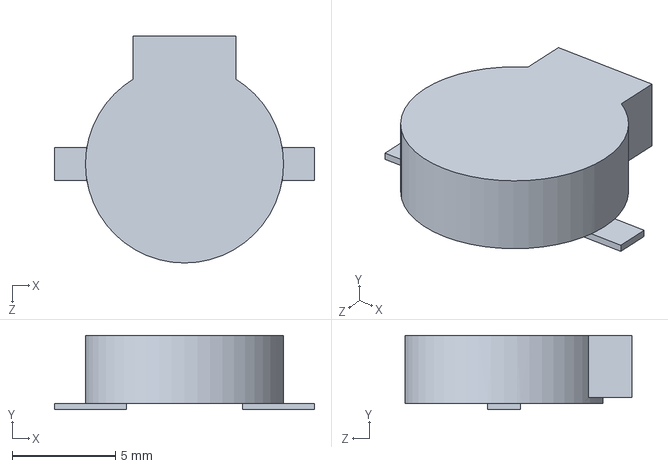
[picture p109: CAD file, 2018-03-09]
SolidWorks/P4.new/P4_BOT-03D PASSIVE BUZZER.SLDPRT
12.6 x 3.60 x 11.0 mm
