glydrfreak/vSpeed-Vario/SolidWorks/P5/V2/CASE_BACK V2.stl

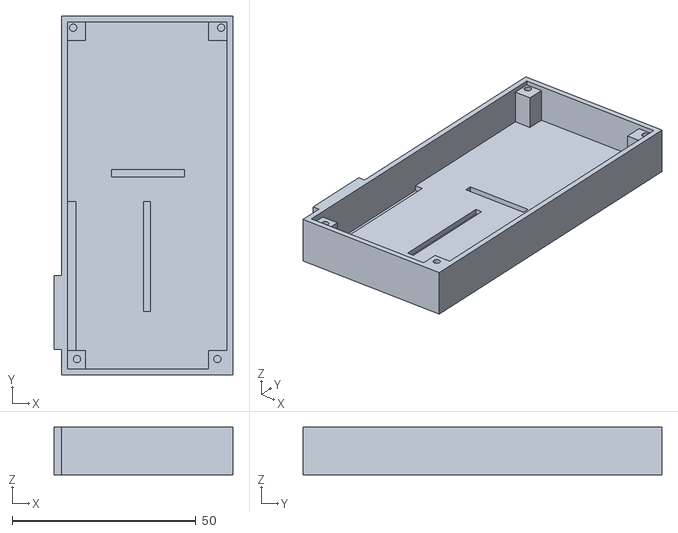
[picture p110: CAD file, 2018-03-19]
SolidWorks/P5/V2/CASE_BACK V2.stl
48.6 x 97.6 x 12.9
