glydrfreak/vSpeed-Vario/SolidWorks/P1.new/P1_CARDBOARD_CASE.SLDPRT

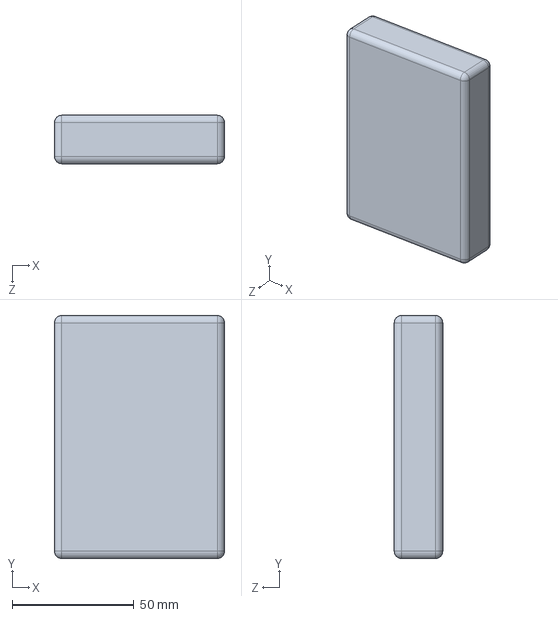
[picture p111: CAD file, 2017-11-29]
SolidWorks/P1.new/P1_CARDBOARD_CASE.SLDPRT
70.0 x 100.0 x 20.0 mm
