glydrfreak/vSpeed-Vario/SolidWorks/P2.new/CUSTOM PCB.SLDPRT

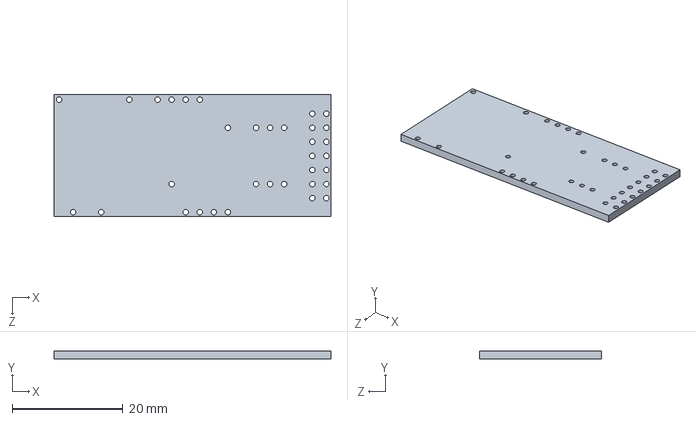
[picture p112: CAD file, 2017-11-29]
SolidWorks/P2.new/CUSTOM PCB.SLDPRT
50.0 x 1.50 x 22.0 mm
