glydrfreak/vSpeed-Vario/SolidWorks/P4.new/P4.1_2.9_EPD_CASE_COVER.SLDPRT

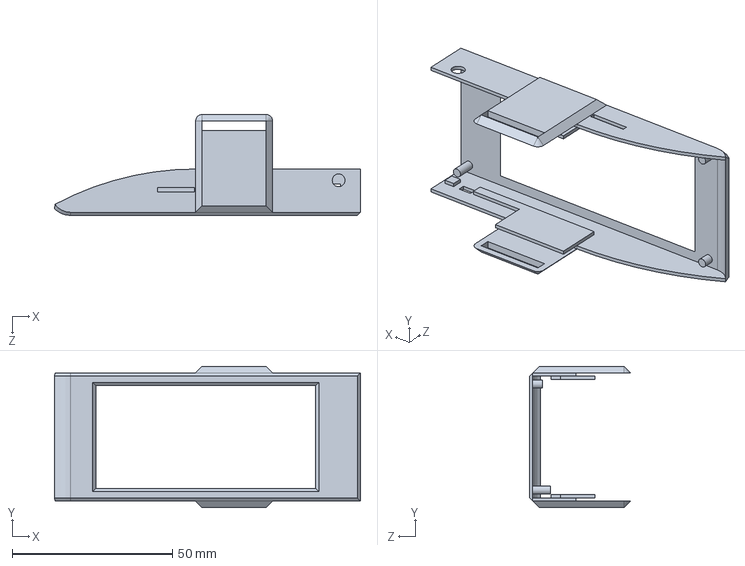
[picture p113: CAD file, 2018-03-09]
SolidWorks/P4.new/P4.1_2.9_EPD_CASE_COVER.SLDPRT
95.4 x 44.0 x 31.5 mm
