glydrfreak/vSpeed-Vario/SolidWorks/P4/P4_SO8.SLDPRT

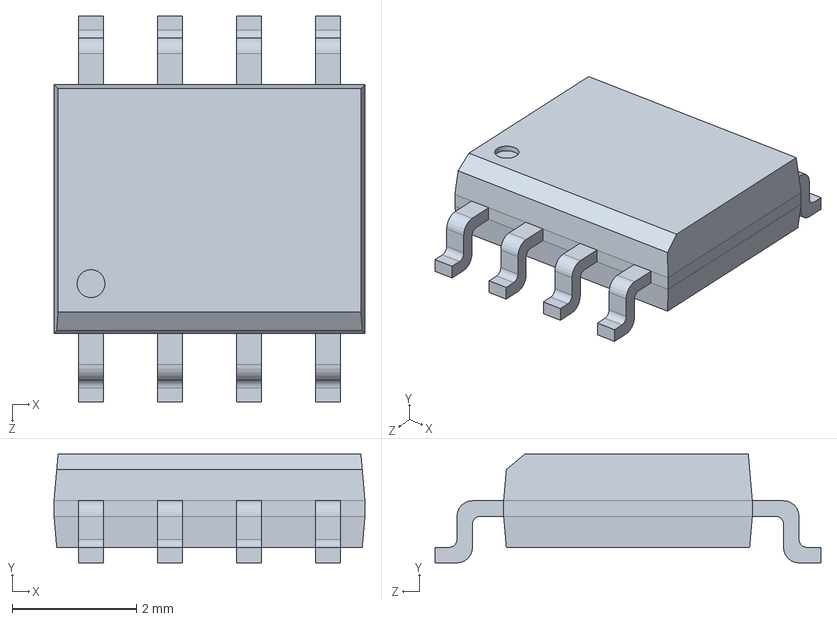
[picture p114: CAD file, 2017-12-11]
SolidWorks/P4/P4_SO8.SLDPRT
5.00 x 1.75 x 6.20 mm
