glydrfreak/vSpeed-Vario/SolidWorks/P1.new/cristal_inferior.SLDPRT

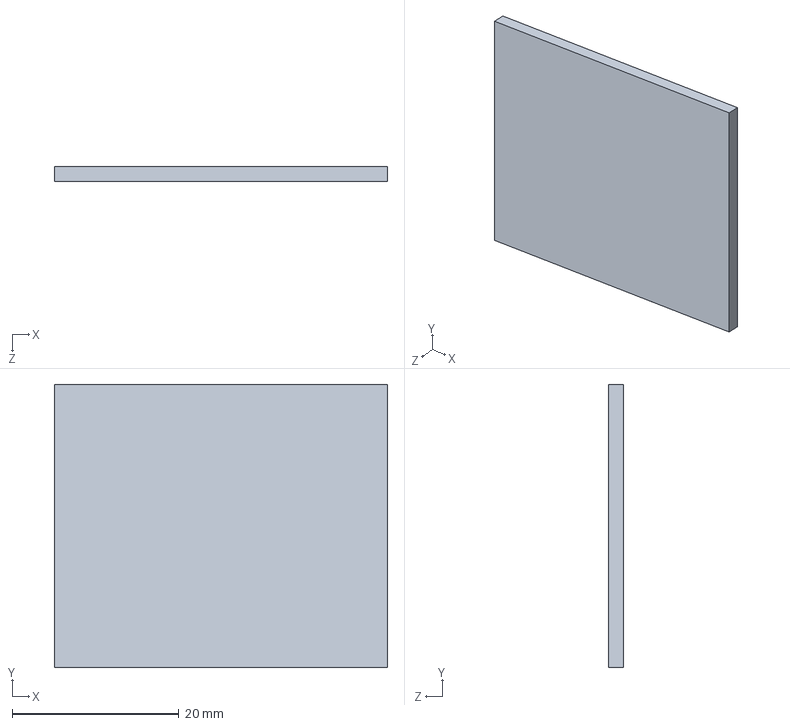
[picture p115: CAD file, 2017-11-29]
SolidWorks/P1.new/cristal_inferior.SLDPRT
40.0 x 34.0 x 1.79 mm
