glydrfreak/vSpeed-Vario/SolidWorks/P2.new/BLUEFRUIT FEATHER.SLDPRT

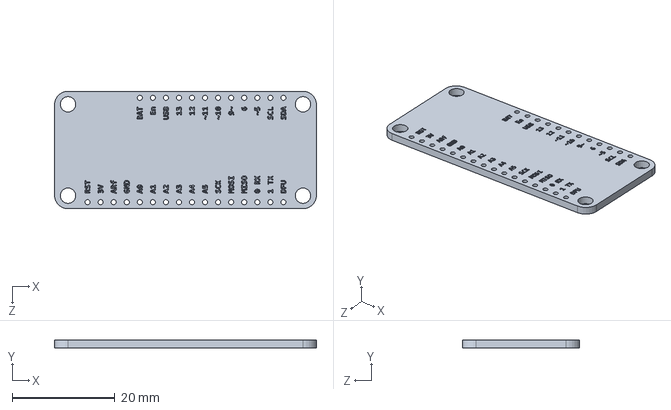
[picture p116: CAD file, 2017-11-29]
SolidWorks/P2.new/BLUEFRUIT FEATHER.SLDPRT
51.0 x 1.50 x 22.9 mm
