glydrfreak/vSpeed-Vario/SolidWorks/P3.new/p3_1 PIN MALE HEADER.SLDPRT

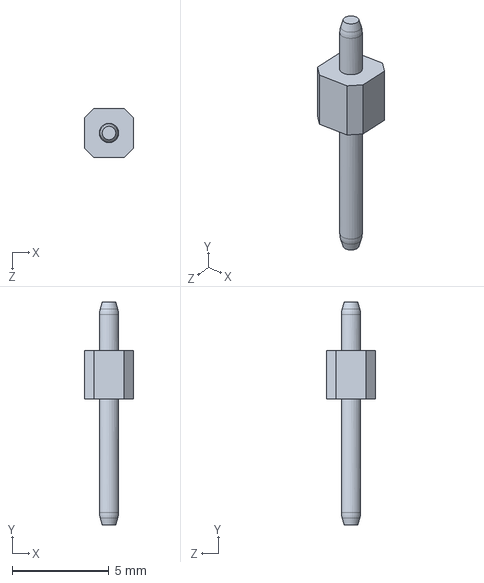
[picture p117: CAD file, 2017-11-29]
SolidWorks/P3.new/p3_1 PIN MALE HEADER.SLDPRT
2.54 x 11.5 x 2.54 mm
