glydrfreak/vSpeed-Vario/SolidWorks/P4.new/P4_JST 2pin rightangle.SLDPRT

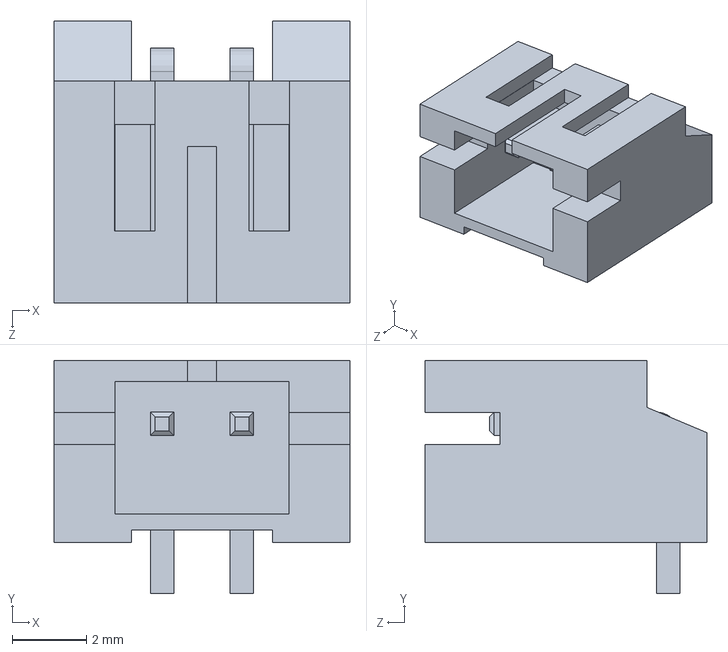
[picture p118: CAD file, 2018-03-09]
SolidWorks/P4.new/P4_JST 2pin rightangle.SLDPRT
8.00 x 6.30 x 7.62 mm
