glydrfreak/vSpeed-Vario/SolidWorks/P4/P4_1PIN_8.25_SHORT_SOCKET.SLDPRT

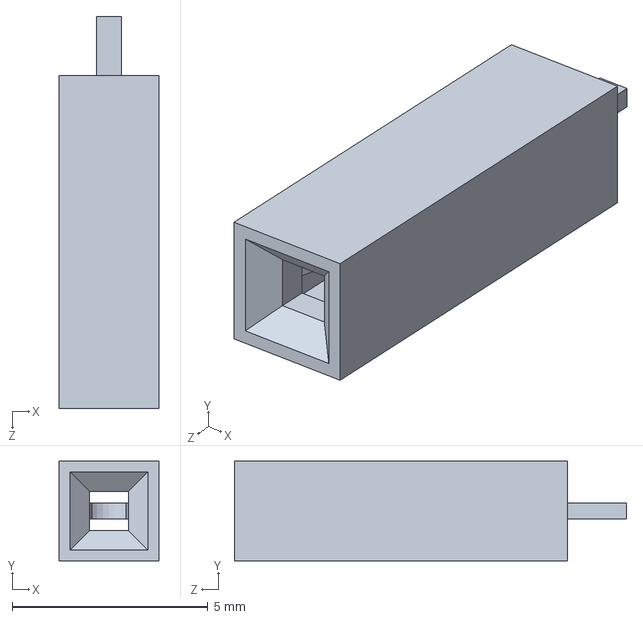
[picture p119: CAD file, 2017-12-11]
SolidWorks/P4/P4_1PIN_8.25_SHORT_SOCKET.SLDPRT
2.54 x 2.54 x 10.0 mm
