glydrfreak/vSpeed-Vario/SolidWorks/P1.new/vidro.SLDPRT

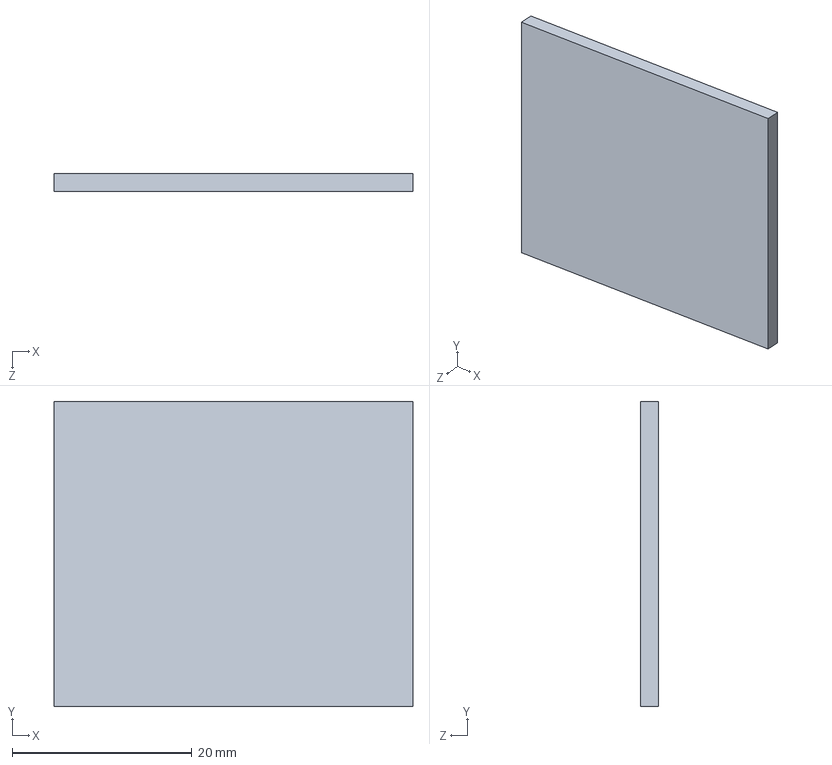
[picture p120: CAD file, 2017-11-29]
SolidWorks/P1.new/vidro.SLDPRT
40.0 x 34.0 x 2.00 mm
