glydrfreak/vSpeed-Vario/SolidWorks/P2.new/SIL_Socket08_.SLDPRT

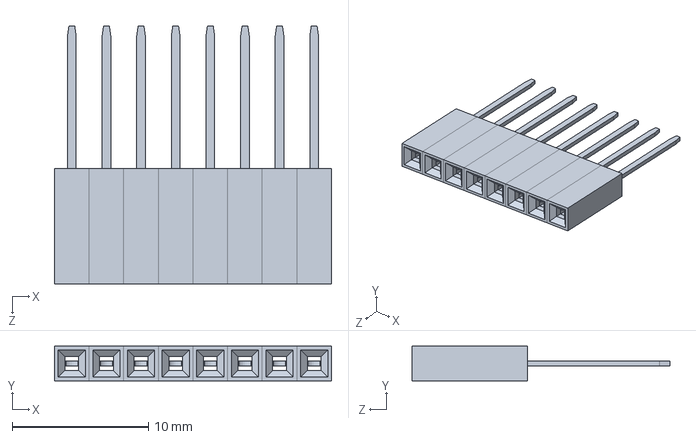
[picture p121: CAD file, 2017-11-29]
SolidWorks/P2.new/SIL_Socket08_.SLDPRT
20.3 x 2.54 x 19.0 mm
