glydrfreak/vSpeed-Vario/SolidWorks/P3.new/p3_MS5611.SLDPRT

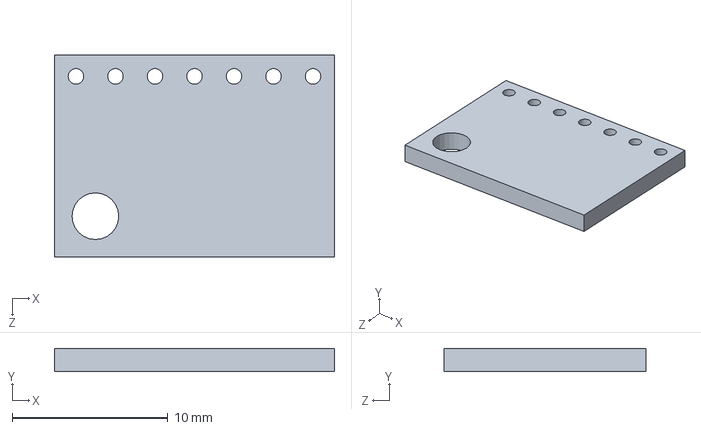
[picture p122: CAD file, 2017-11-29]
SolidWorks/P3.new/p3_MS5611.SLDPRT
18.0 x 1.50 x 13.0 mm
