glydrfreak/vSpeed-Vario/SolidWorks/P4/P4_SMT_RA_PIN.SLDPRT

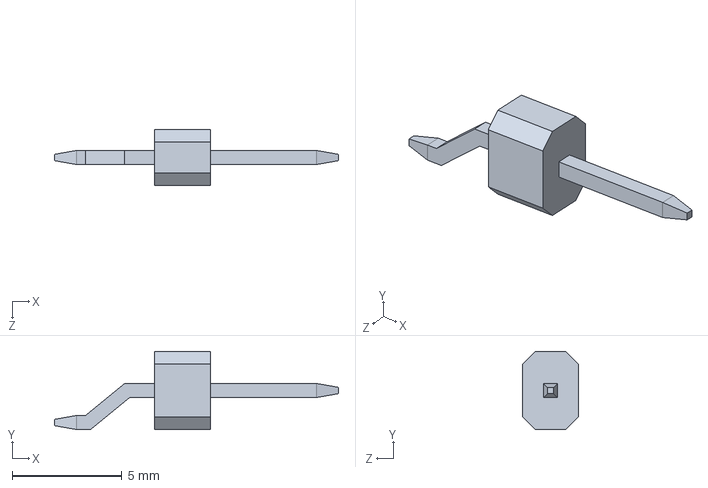
[picture p123: CAD file, 2017-12-11]
SolidWorks/P4/P4_SMT_RA_PIN.SLDPRT
12.9 x 3.56 x 2.54 mm
