glydrfreak/vSpeed-Vario/SolidWorks/P1.new/8pin_header.SLDPRT

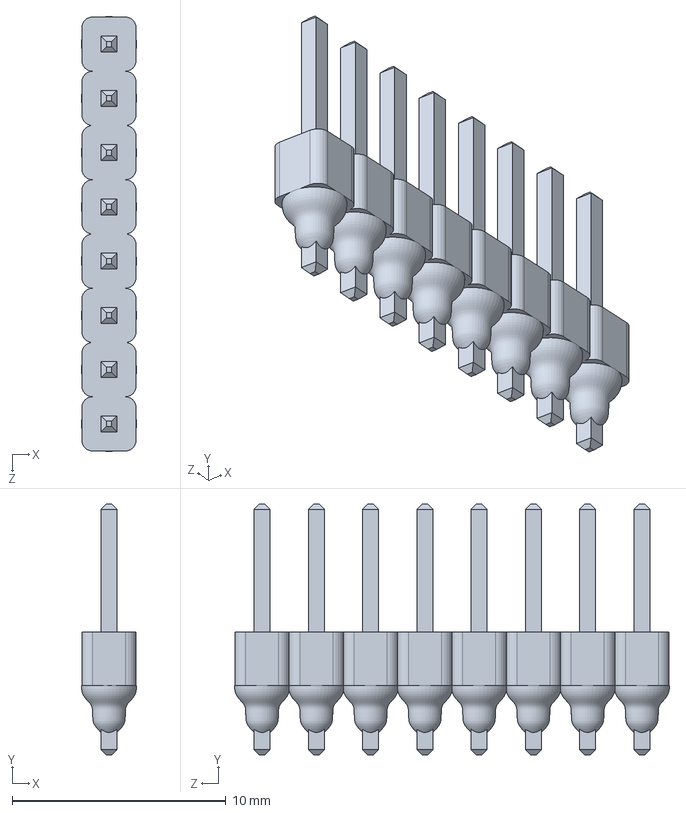
[picture p124: CAD file, 2017-11-29]
SolidWorks/P1.new/8pin_header.SLDPRT
2.58 x 11.8 x 20.4 mm
