glydrfreak/vSpeed-Vario/SolidWorks/P3.new/P3_BACK_COVER.SLDPRT

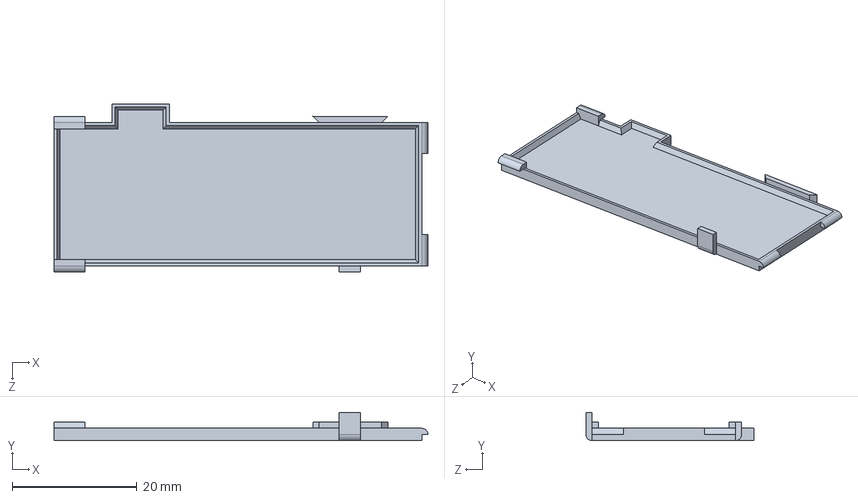
[picture p125: CAD file, 2017-11-29]
SolidWorks/P3.new/P3_BACK_COVER.SLDPRT
60.0 x 4.55 x 27.0 mm
