glydrfreak/vSpeed-Vario/SolidWorks/P4/HARNESS.SLDPRT

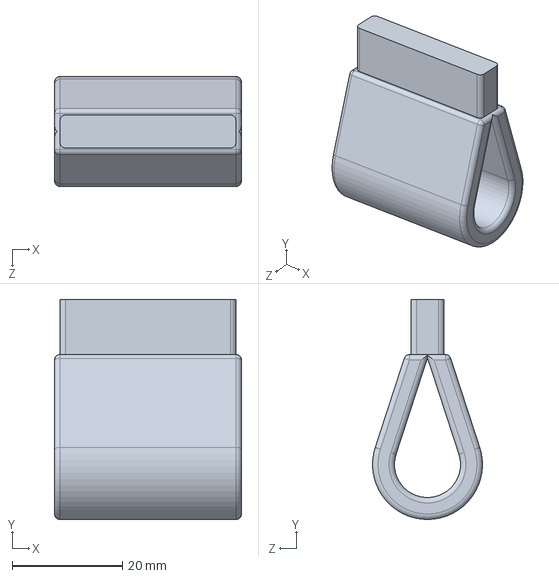
[picture p126: CAD file, 2017-12-11]
SolidWorks/P4/HARNESS.SLDPRT
34.0 x 40.0 x 20.0 mm
