glydrfreak/vSpeed-Vario/SolidWorks/P4.new/P4_MICRO_SD_WITH_SLOT.SLDPRT

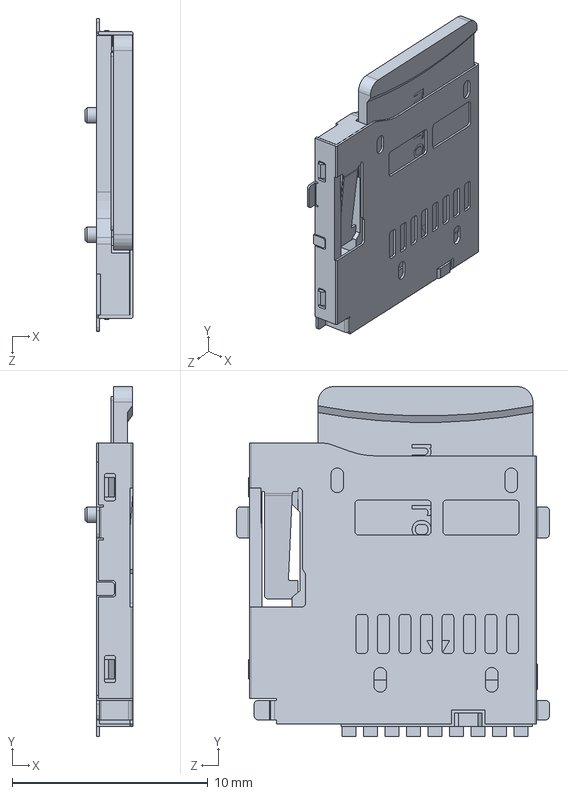
[picture p127: CAD file, 2018-03-09]
SolidWorks/P4.new/P4_MICRO_SD_WITH_SLOT.SLDPRT
2.44 x 17.9 x 16.0 mm
