glydrfreak/vSpeed-Vario/SolidWorks/P4.new/P4_AB2_USB_MICRO_SMD.SLDPRT

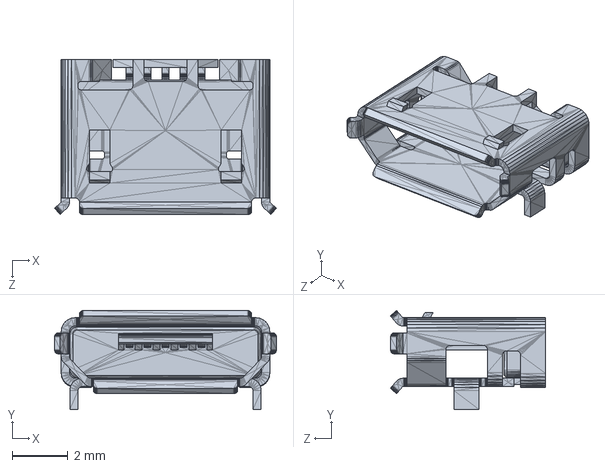
[picture p128: CAD file, 2018-03-09]
SolidWorks/P4.new/P4_AB2_USB_MICRO_SMD.SLDPRT
7.99 x 3.56 x 5.59 mm
