glydrfreak/vSpeed-Vario/SolidWorks/P4/P4_soic-14.SLDPRT

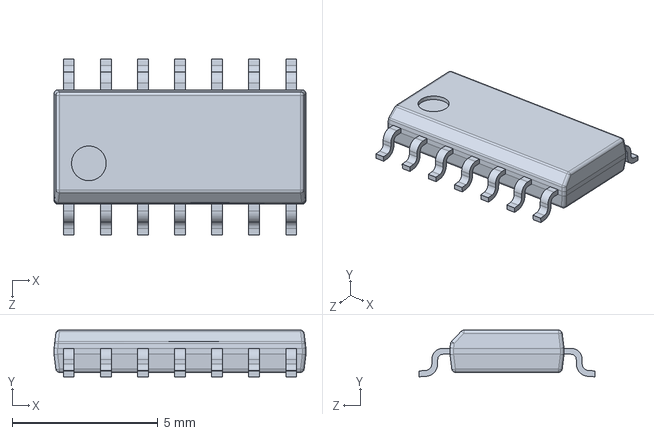
[picture p129: CAD file, 2017-12-11]
SolidWorks/P4/P4_soic-14.SLDPRT
8.64 x 1.60 x 6.05 mm
