glydrfreak/vSpeed-Vario/SolidWorks/P3.new/p3_SS12D00G4 1P2T Bent.SLDPRT

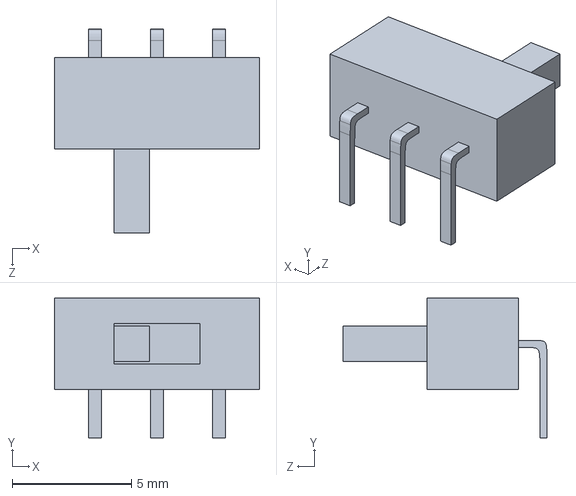
[picture p130: CAD file, 2017-11-29]
SolidWorks/P3.new/p3_SS12D00G4 1P2T Bent.SLDPRT
8.61 x 5.88 x 8.57 mm
