glydrfreak/vSpeed-Vario/SolidWorks/P4.new/P4_BTG 3.7V 150mAh LIPO.SLDPRT

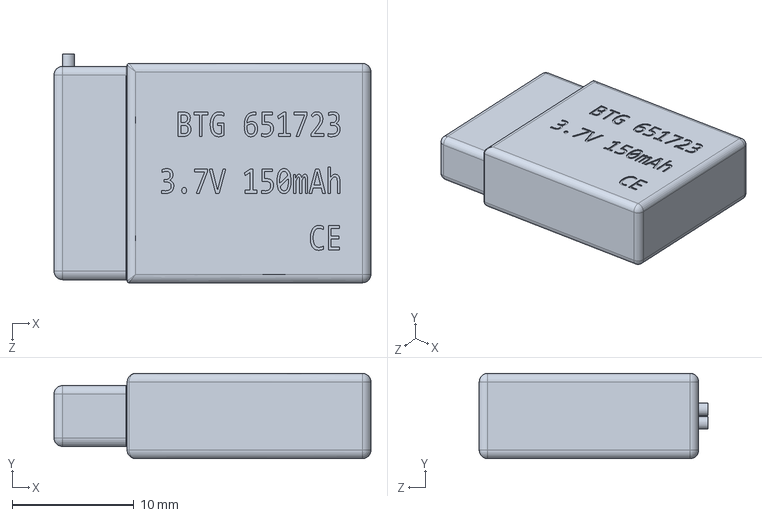
[picture p131: CAD file, 2018-03-09]
SolidWorks/P4.new/P4_BTG 3.7V 150mAh LIPO.SLDPRT
26.0 x 7.00 x 18.8 mm
