glydrfreak/vSpeed-Vario/SolidWorks/P4/P4_2.9_EPD_CASE_BACK.SLDPRT

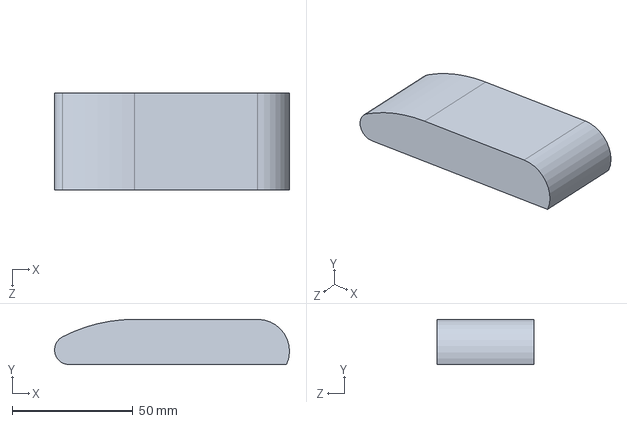
[picture p132: CAD file, 2017-12-11]
SolidWorks/P4/P4_2.9_EPD_CASE_BACK.SLDPRT
97.2 x 18.7 x 40.0 mm
