glydrfreak/vSpeed-Vario/SolidWorks/P2.new/P2 CASE - BACK COVER.SLDPRT

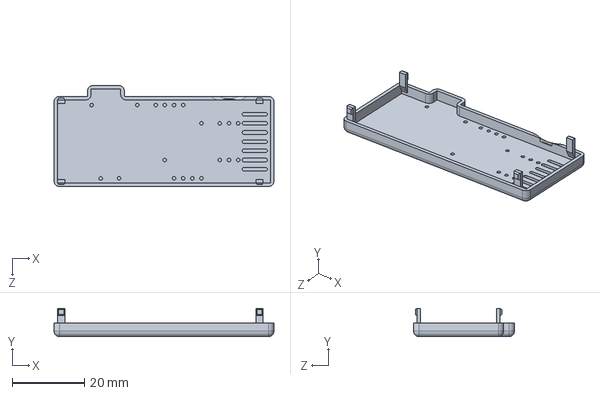
[picture p133: CAD file, 2017-11-29]
SolidWorks/P2.new/P2 CASE - BACK COVER.SLDPRT
61.0 x 7.80 x 28.0 mm
