glydrfreak/vSpeed-Vario/SolidWorks/P4.new/P4_SPACER.SLDPRT

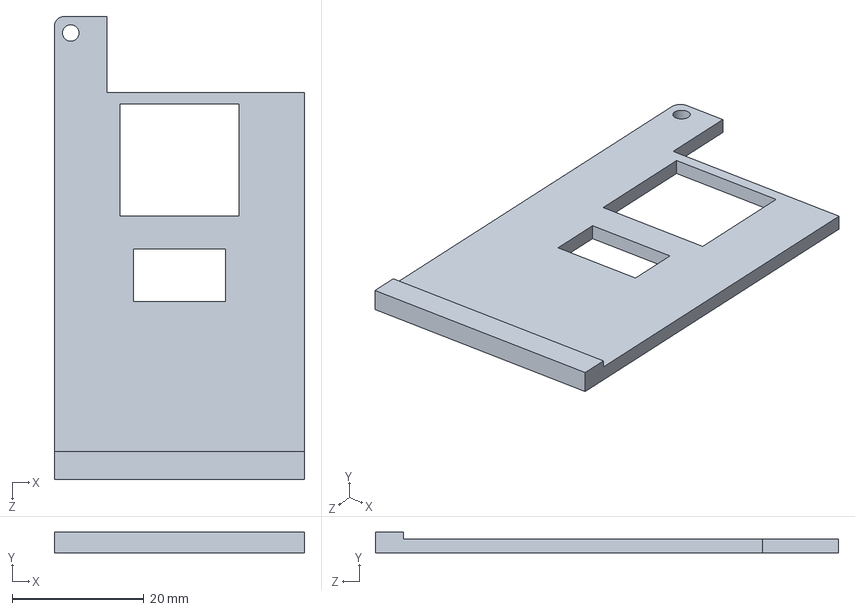
[picture p134: CAD file, 2018-03-09]
SolidWorks/P4.new/P4_SPACER.SLDPRT
38.0 x 3.13 x 70.2 mm
