glydrfreak/vSpeed-Vario/SolidWorks/P4/P4_2.9_EPD_CASE_COVER.SLDPRT

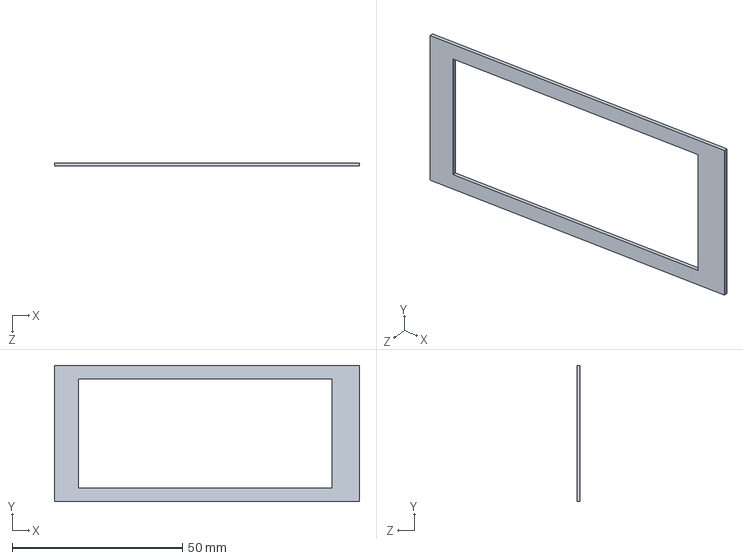
[picture p135: CAD file, 2017-12-11]
SolidWorks/P4/P4_2.9_EPD_CASE_COVER.SLDPRT
89.5 x 40.0 x 1.00 mm
