glydrfreak/vSpeed-Vario/SolidWorks/P3.new/p3_CASE - FRONT SHELL.SLDPRT

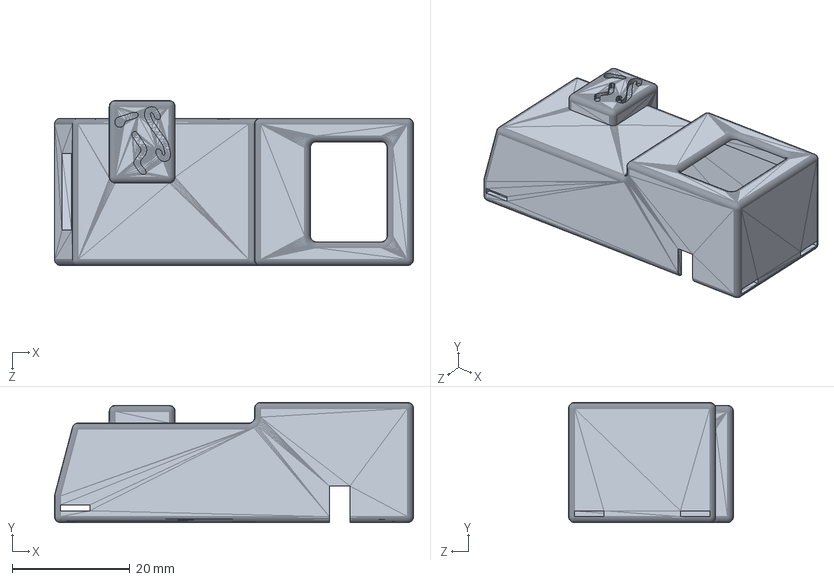
[picture p136: CAD file, 2017-11-29]
SolidWorks/P3.new/p3_CASE - FRONT SHELL.SLDPRT
61.0 x 20.4 x 28.0 mm
