glydrfreak/vSpeed-Vario/SolidWorks/P2.new/2 PIN MALE HEADER.SLDPRT

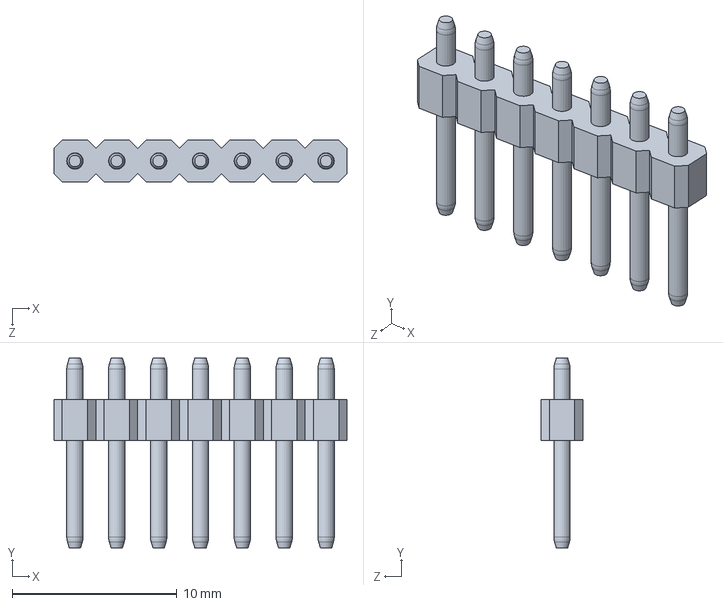
[picture p137: CAD file, 2017-11-29]
SolidWorks/P2.new/2 PIN MALE HEADER.SLDPRT
17.8 x 11.5 x 2.54 mm
