glydrfreak/vSpeed-Vario/SolidWorks/P4/RISER.SLDPRT

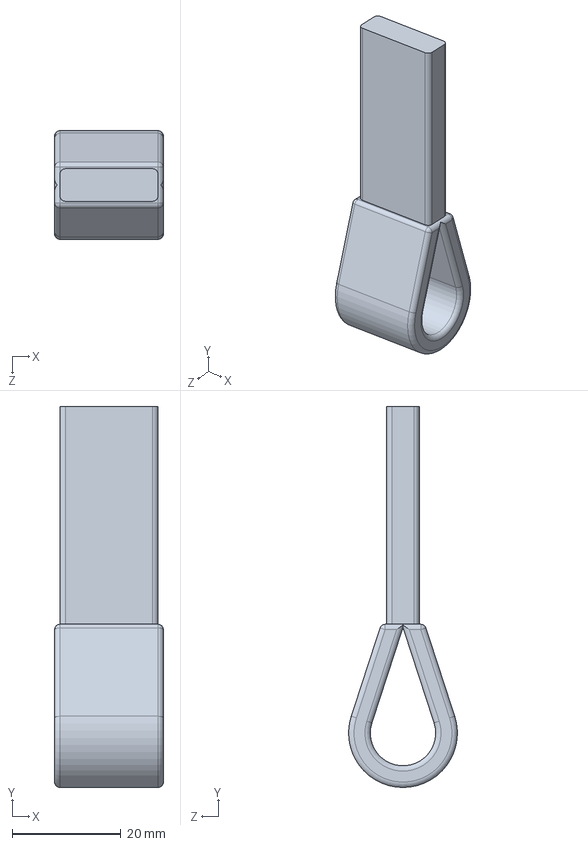
[picture p138: CAD file, 2017-12-11]
SolidWorks/P4/RISER.SLDPRT
20.0 x 70.0 x 20.0 mm
