glydrfreak/vSpeed-Vario/SolidWorks/P4.new/P4.1_CASE_RIGHT.SLDPRT

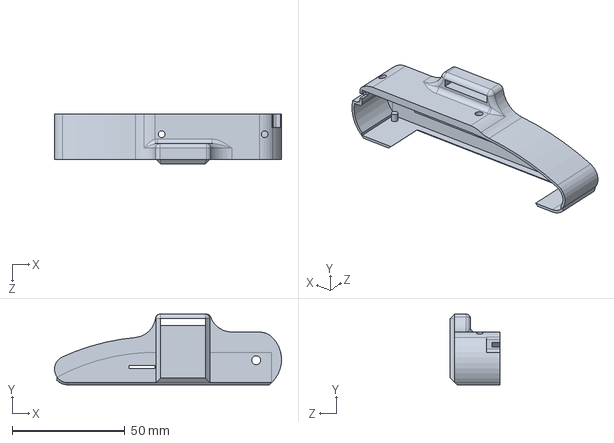
[picture p139: CAD file, 2018-03-09]
SolidWorks/P4.new/P4.1_CASE_RIGHT.SLDPRT
100.8 x 31.5 x 22.0 mm
