glydrfreak/vSpeed-Vario/SolidWorks/P4.new/P4_CAPC-0805-T1.35-BN.SLDPRT

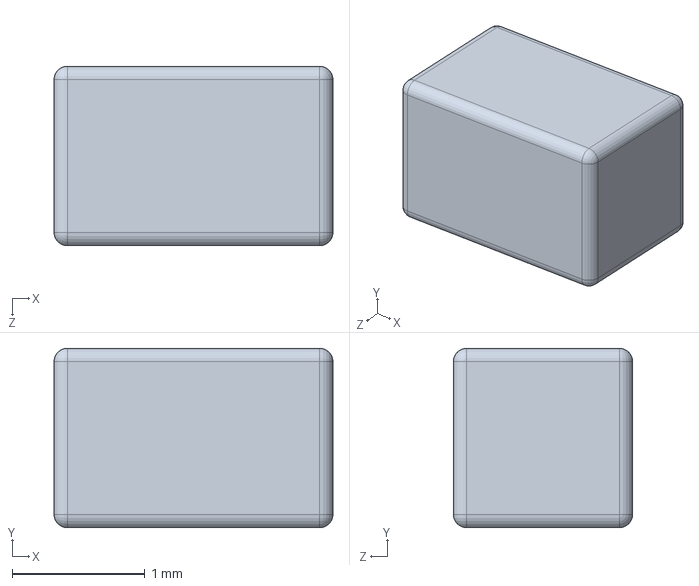
[picture p140: CAD file, 2018-03-09]
SolidWorks/P4.new/P4_CAPC-0805-T1.35-BN.SLDPRT
2.10 x 1.35 x 1.35 mm
