glydrfreak/vSpeed-Vario/SolidWorks/P4/P4_RESC-0805.SLDPRT

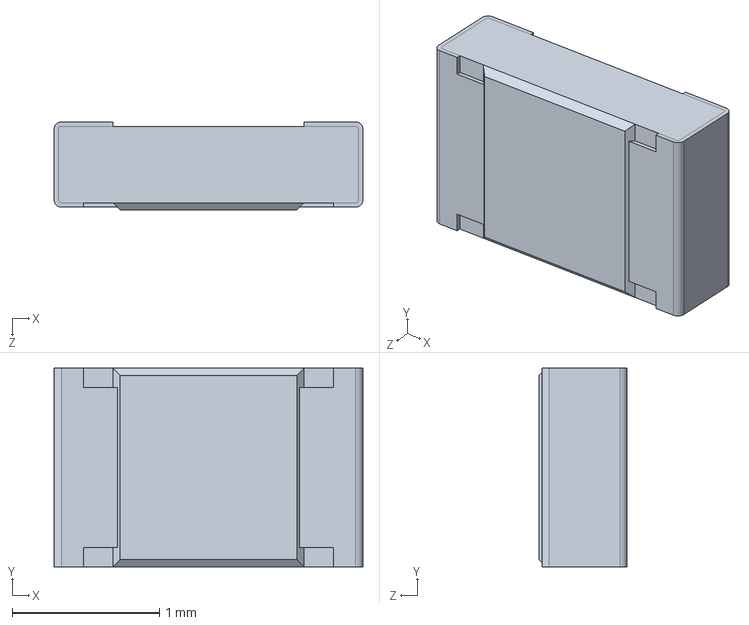
[picture p141: CAD file, 2017-12-11]
SolidWorks/P4/P4_RESC-0805.SLDPRT
2.10 x 1.35 x 0.6 mm
