glydrfreak/vSpeed-Vario/SolidWorks/P4.new/P4.1_2.9_EPD_CASE_BACK.SLDPRT

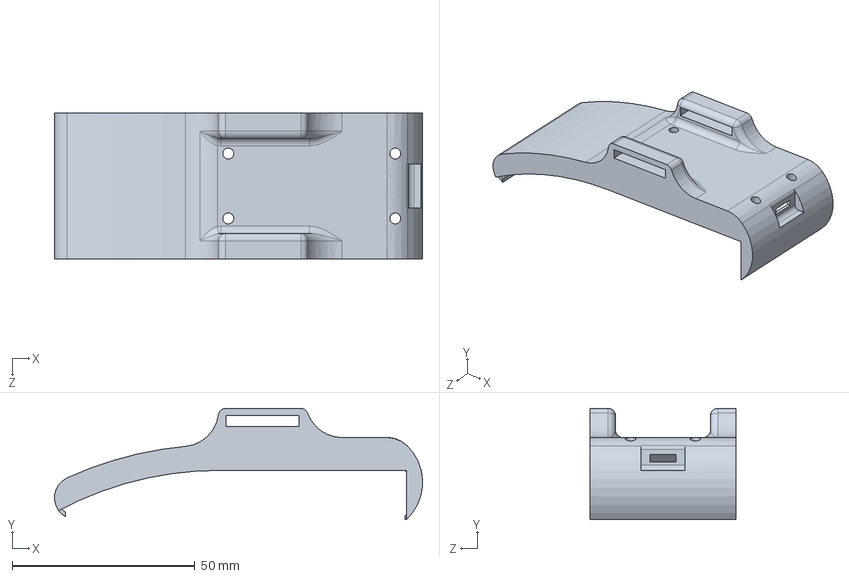
[picture p142: CAD file, 2018-03-09]
SolidWorks/P4.new/P4.1_2.9_EPD_CASE_BACK.SLDPRT
100.8 x 30.5 x 40.0 mm
