glydrfreak/vSpeed-Vario/SolidWorks/P4/P4_TACTILE_SWITCH_SIDE.SLDPRT

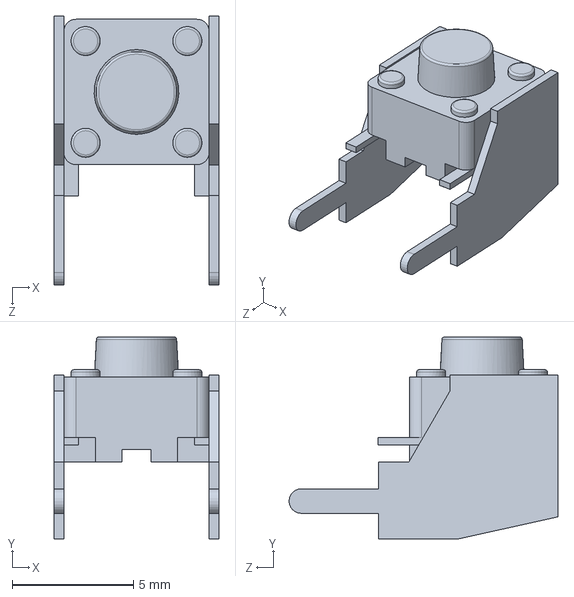
[picture p143: CAD file, 2017-12-11]
SolidWorks/P4/P4_TACTILE_SWITCH_SIDE.SLDPRT
6.80 x 8.34 x 11.1 mm
