glydrfreak/vSpeed-Vario/SolidWorks/P4/P4_SPACER.SLDPRT

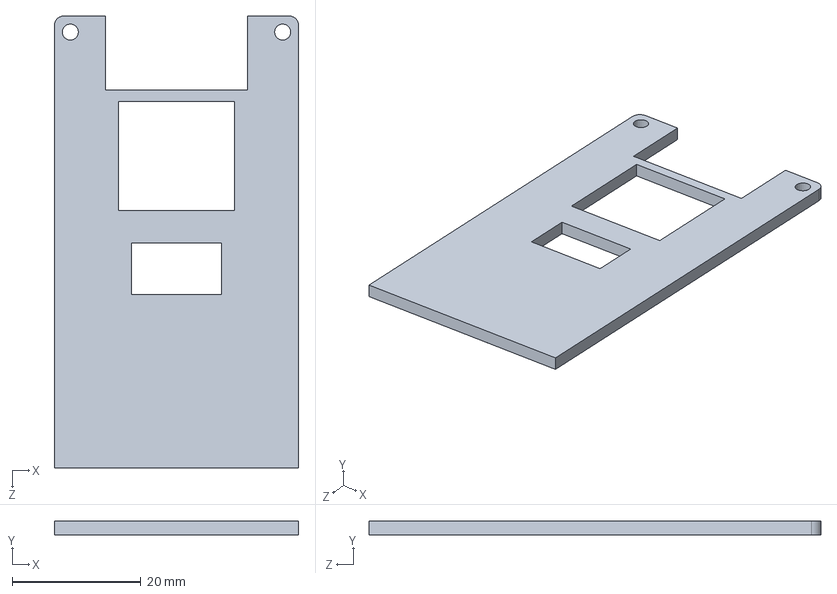
[picture p144: CAD file, 2017-12-11]
SolidWorks/P4/P4_SPACER.SLDPRT
38.0 x 2.13 x 70.2 mm
