glydrfreak/vSpeed-Vario/SolidWorks/P4/P4_FPC_24.SLDPRT

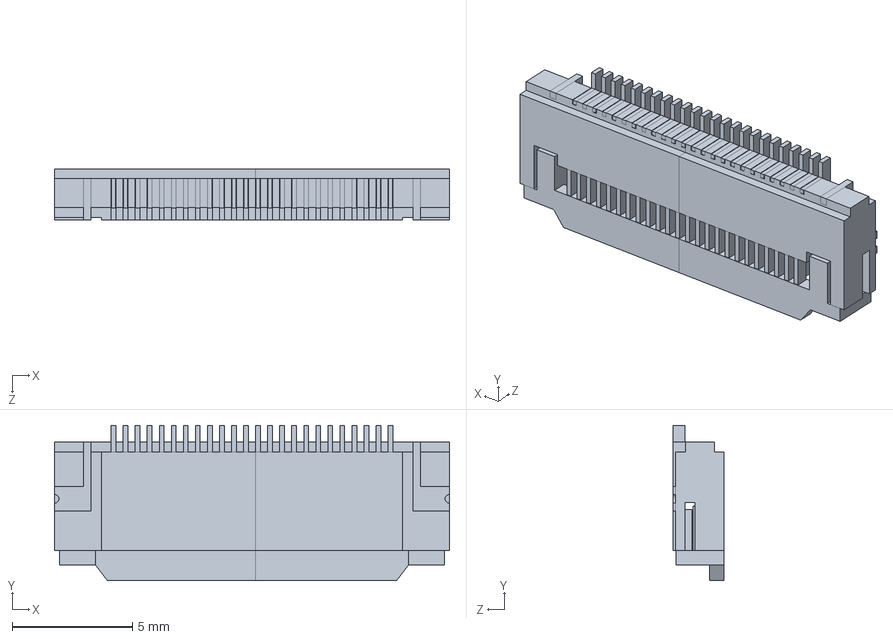
[picture p145: CAD file, 2017-12-11]
SolidWorks/P4/P4_FPC_24.SLDPRT
16.4 x 6.45 x 2.13 mm
