glydrfreak/vSpeed-Vario/SolidWorks/P4/P4_SOT23.SLDPRT

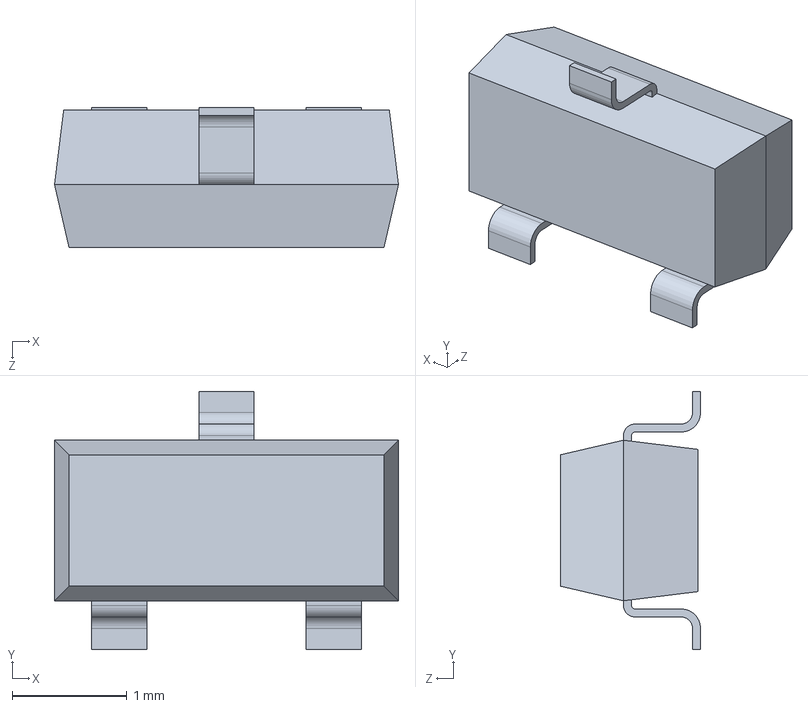
[picture p146: CAD file, 2017-12-11]
SolidWorks/P4/P4_SOT23.SLDPRT
3.00 x 2.25 x 1.22 mm
