glydrfreak/vSpeed-Vario/SolidWorks/P4/GATILHO.SLDPRT

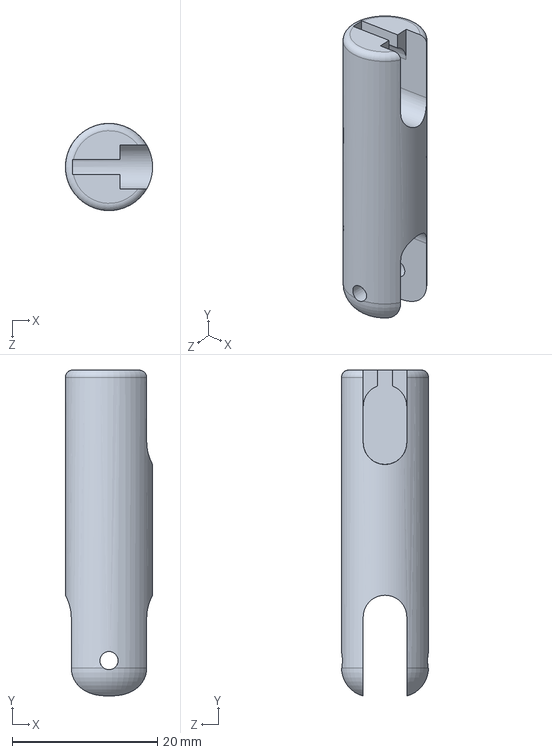
[picture p147: CAD file, 2017-11-25]
SolidWorks/P4/GATILHO.SLDPRT
12.0 x 44.9 x 12.0 mm
