glydrfreak/vSpeed-Vario/SolidWorks/P4/P4_MOUNTINT_BRACKET.SLDPRT

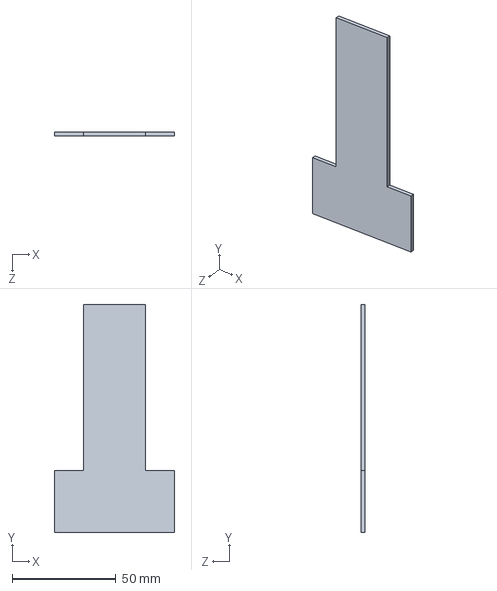
[picture p148: CAD file, 2017-11-23]
SolidWorks/P4/P4_MOUNTINT_BRACKET.SLDPRT
58.0 x 110.0 x 2.00 mm
