glydrfreak/vSpeed-Vario/SolidWorks/P4/P4_MOUNTING_BRACKET.SLDPRT

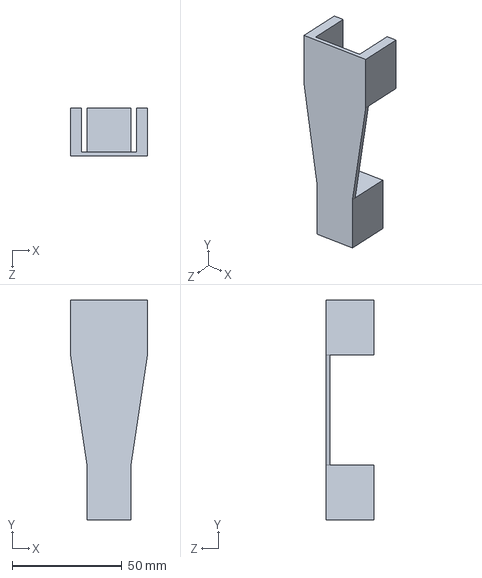
[picture p149: CAD file, 2017-11-23]
SolidWorks/P4/P4_MOUNTING_BRACKET.SLDPRT
35.0 x 100.0 x 22.0 mm
