glydrfreak/vSpeed-Vario/SolidWorks/P4/P4_MOUNTING_BRACKET3.SLDPRT

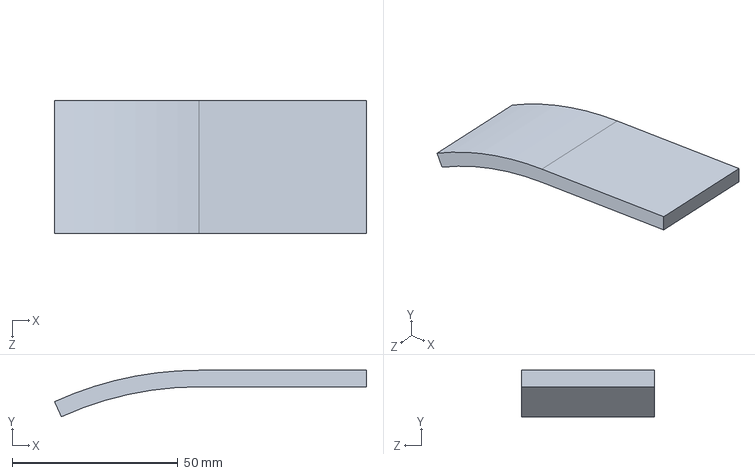
[picture p150: CAD file, 2017-11-23]
SolidWorks/P4/P4_MOUNTING_BRACKET3.SLDPRT
94.1 x 14.0 x 40.0 mm
