glydrfreak/vSpeed-Vario/SolidWorks/P4/MOUNTING_BRACKET_PIN.SLDPRT

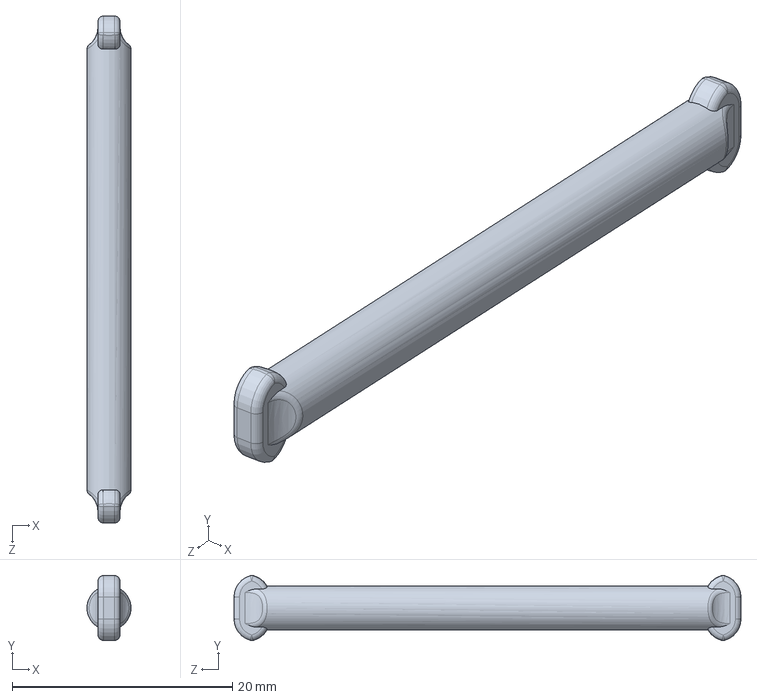
[picture p151: CAD file, 2017-11-23]
SolidWorks/P4/MOUNTING_BRACKET_PIN.SLDPRT
4.00 x 5.91 x 46.0 mm
