glydrfreak/vSpeed-Vario/SolidWorks/P4/P4_MOUNTING_BRACKET2.SLDPRT

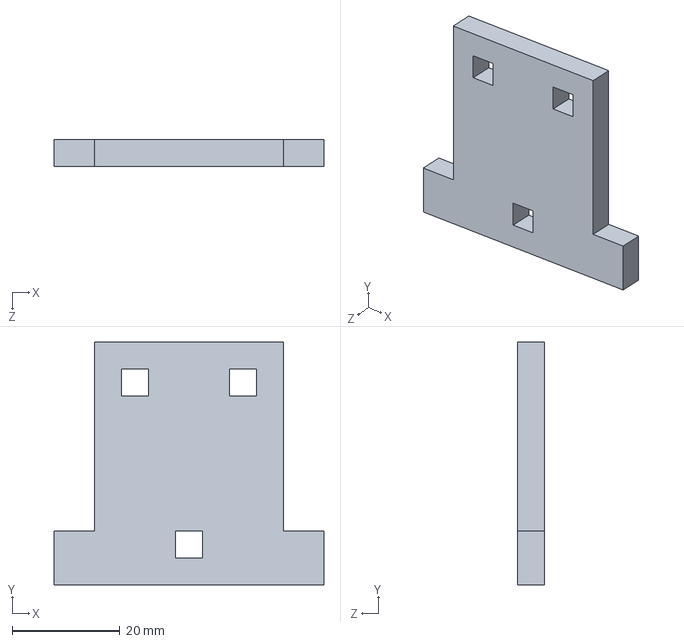
[picture p152: CAD file, 2017-11-23]
SolidWorks/P4/P4_MOUNTING_BRACKET2.SLDPRT
50.0 x 45.0 x 5.00 mm
