glydrfreak/vSpeed-Vario/SolidWorks/P4.new/P4.1_CASE_LEFT.SLDPRT

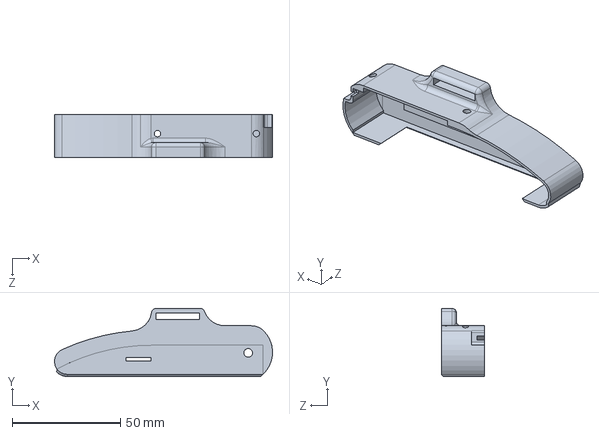
[picture p153: CAD file, 2018-03-09]
SolidWorks/P4.new/P4.1_CASE_LEFT.SLDPRT
100.8 x 31.5 x 20.0 mm
