glydrfreak/vSpeed-Vario/SolidWorks/P4.new/P4_SOLDER_STENCIL.SLDPRT

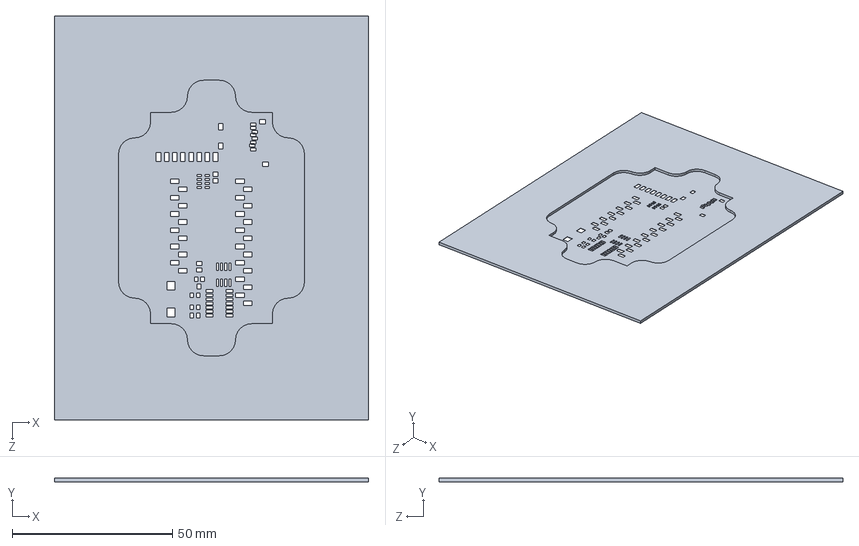
[picture p154: CAD file, 2017-11-23]
SolidWorks/P4.new/P4_SOLDER_STENCIL.SLDPRT
98.0 x 1.12 x 126.0 mm
