glydrfreak/vSpeed-Vario/SolidWorks/P4/P4_DIP8N.SLDPRT

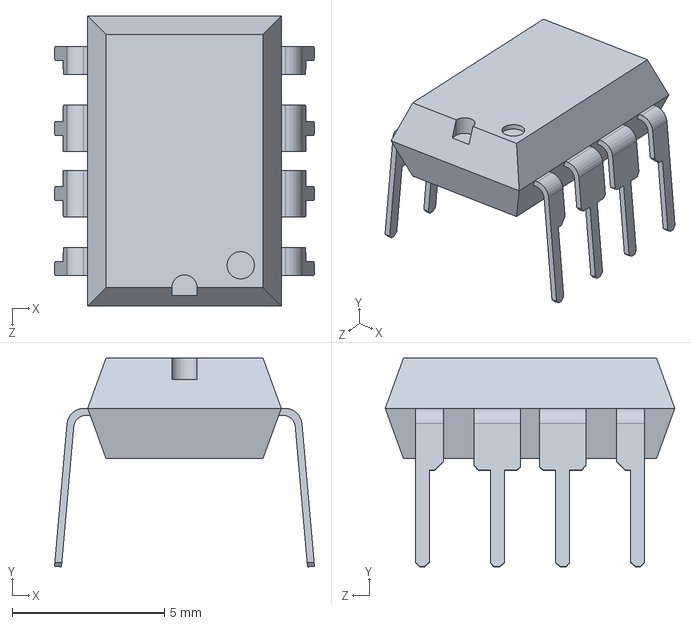
[picture p155: CAD file, 2017-11-22]
SolidWorks/P4/P4_DIP8N.SLDPRT
8.53 x 6.85 x 9.50 mm
