glydrfreak/vSpeed-Vario/SolidWorks/P4/P4_EPD_2.13.SLDPRT

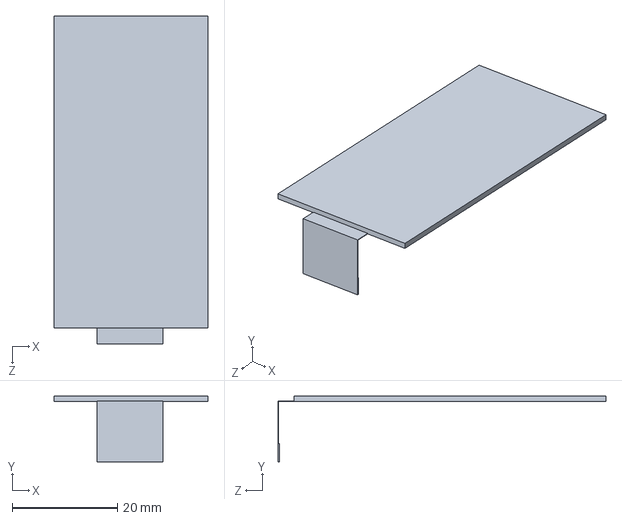
[picture p156: CAD file, 2017-11-22]
SolidWorks/P4/P4_EPD_2.13.SLDPRT
29.2 x 12.4 x 62.2 mm
