glydrfreak/vSpeed-Vario/SolidWorks/P4/P4_PCB.SLDPRT

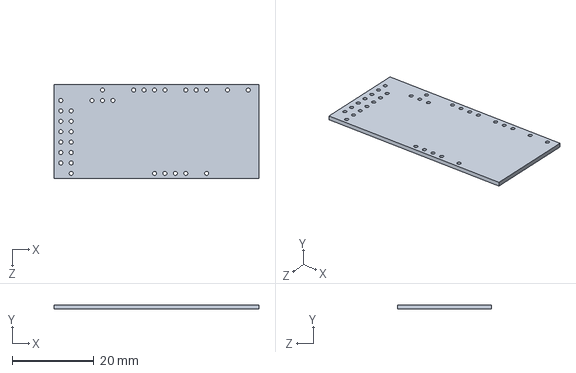
[picture p157: CAD file, 2017-11-22]
SolidWorks/P4/P4_PCB.SLDPRT
50.0 x 1.00 x 23.0 mm
