glydrfreak/vSpeed-Vario/SolidWorks/P4/P4_SHORT_SOCKET.SLDPRT

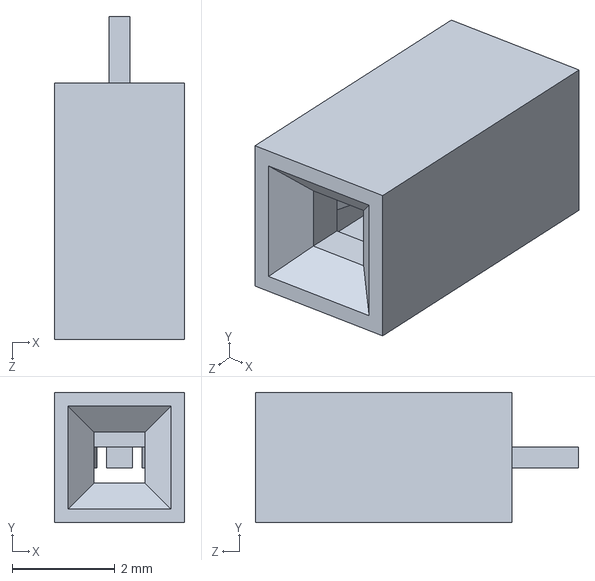
[picture p158: CAD file, 2017-11-22]
SolidWorks/P4/P4_SHORT_SOCKET.SLDPRT
2.54 x 2.54 x 6.29 mm
