glydrfreak/vSpeed-Vario/SolidWorks/P4/P4_EPAPER_CASE.SLDPRT

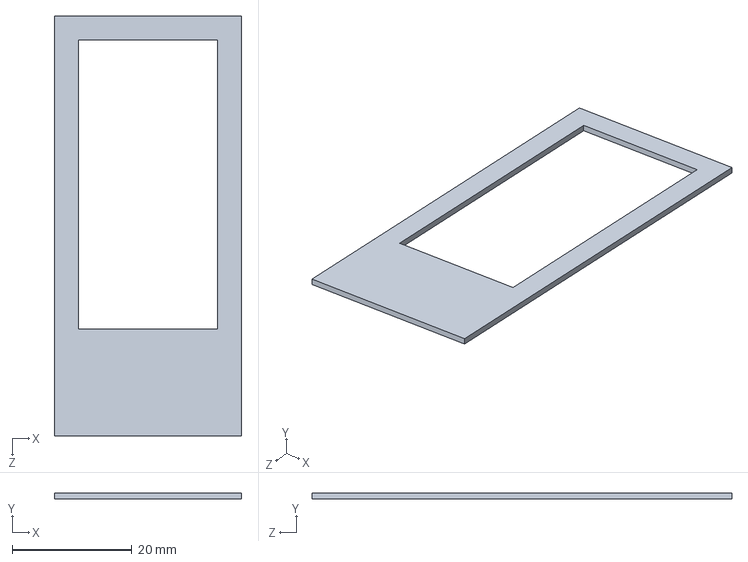
[picture p159: CAD file, 2017-11-22]
SolidWorks/P4/P4_EPAPER_CASE.SLDPRT
31.2 x 1.00 x 70.0 mm
