glydrfreak/vSpeed-Vario/SolidWorks/P4/P4_0.66 INCH OLED.SLDPRT

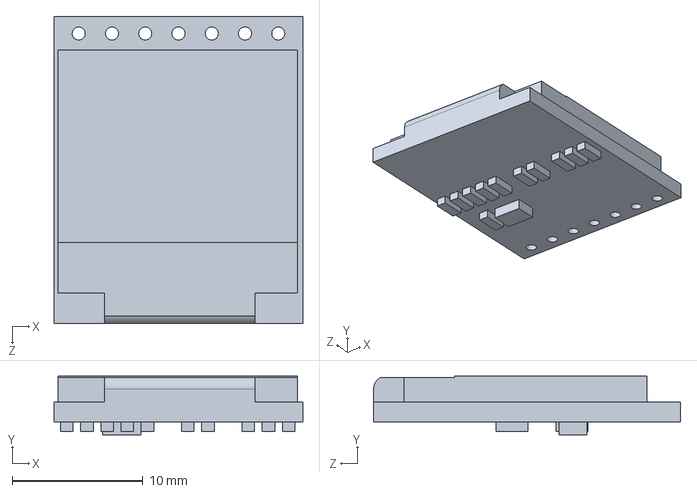
[picture p160: CAD file, 2017-11-22]
SolidWorks/P4/P4_0.66 INCH OLED.SLDPRT
19.0 x 4.50 x 23.4 mm
