glydrfreak/vSpeed-Vario/SolidWorks/P4/P4_BLANK_PCB.SLDPRT

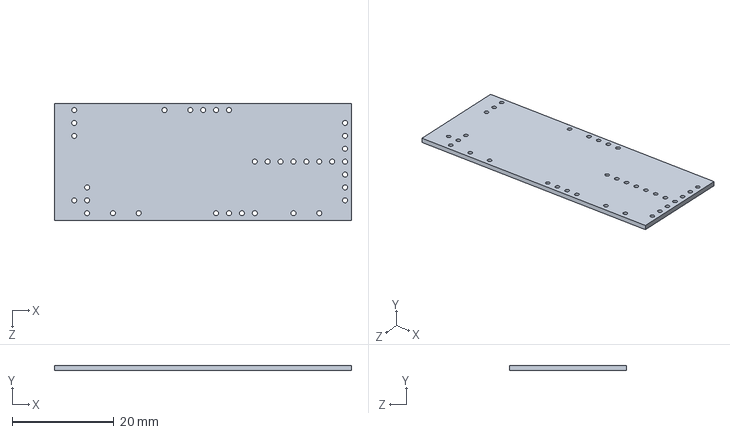
[picture p161: CAD file, 2017-11-22]
SolidWorks/P4/P4_BLANK_PCB.SLDPRT
58.5 x 1.00 x 23.0 mm
