glydrfreak/vSpeed-Vario/SolidWorks/P4/P4_MS5611.SLDPRT

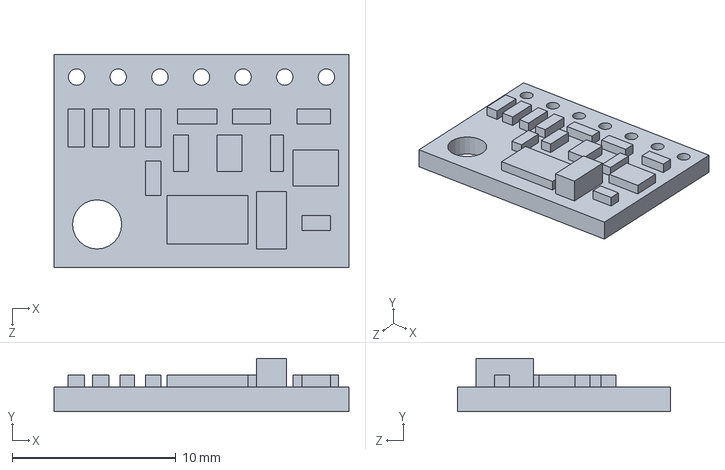
[picture p162: CAD file, 2017-11-22]
SolidWorks/P4/P4_MS5611.SLDPRT
18.0 x 3.25 x 13.0 mm
