glydrfreak/vSpeed-Vario/SolidWorks/P4/P4_VERT_THUMBWHEEL.SLDPRT

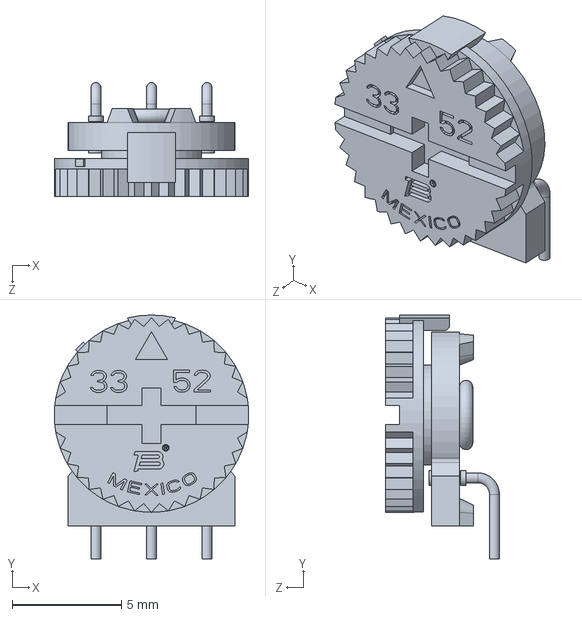
[picture p163: CAD file, 2017-11-22]
SolidWorks/P4/P4_VERT_THUMBWHEEL.SLDPRT
8.88 x 11.2 x 5.21 mm
