glydrfreak/vSpeed-Vario/SolidWorks/P4/P4_SMT0931.SLDPRT

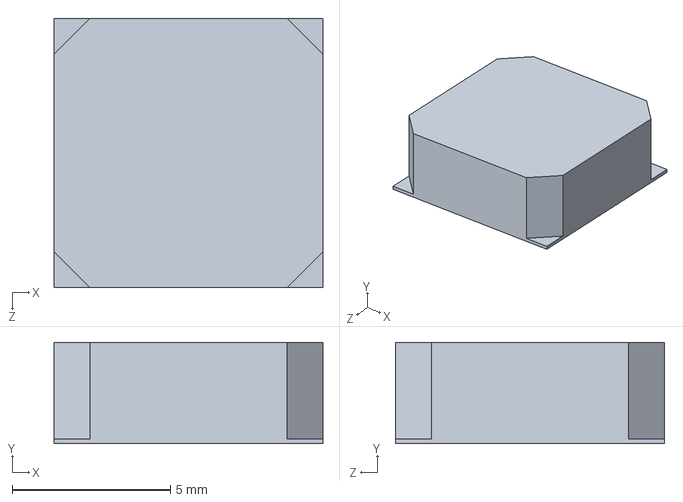
[picture p164: CAD file, 2017-11-22]
SolidWorks/P4/P4_SMT0931.SLDPRT
8.50 x 3.20 x 8.50 mm
