glydrfreak/vSpeed-Vario/SolidWorks/P4/P4_TSSOP-08.SLDPRT

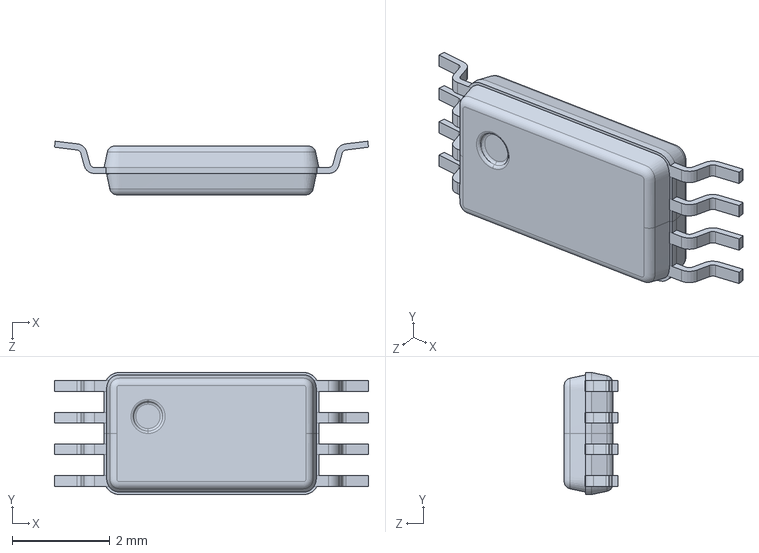
[picture p165: CAD file, 2017-11-22]
SolidWorks/P4/P4_TSSOP-08.SLDPRT
6.43 x 2.50 x 1.10 mm
