glydrfreak/vSpeed-Vario/SolidWorks/P4/P4_RIGHT_ANGLE_7PIN.SLDPRT

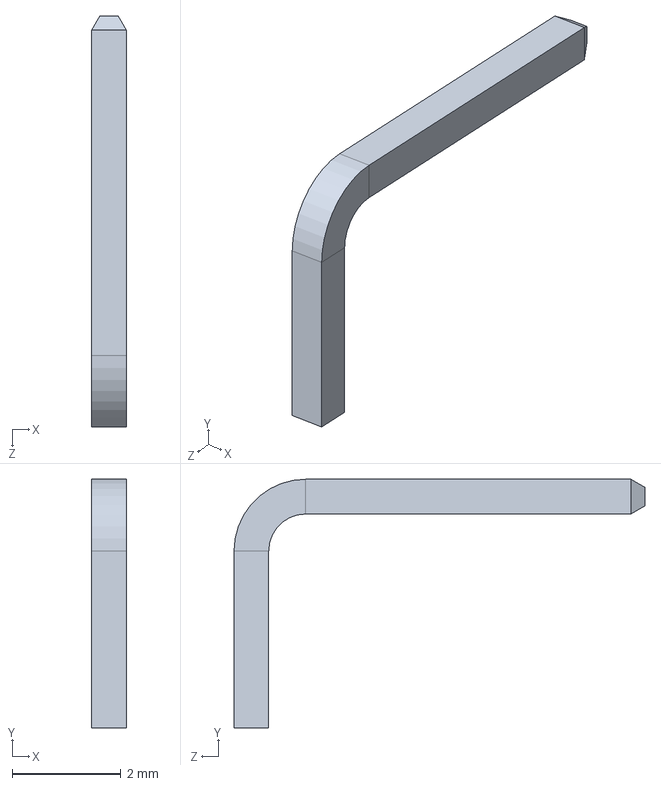
[picture p166: CAD file, 2017-11-03]
SolidWorks/P4/P4_RIGHT_ANGLE_7PIN.SLDPRT
0.64 x 4.58 x 7.57 mm
