glydrfreak/vSpeed-Vario/SolidWorks/P4/P4_SD_Adapter.SLDPRT

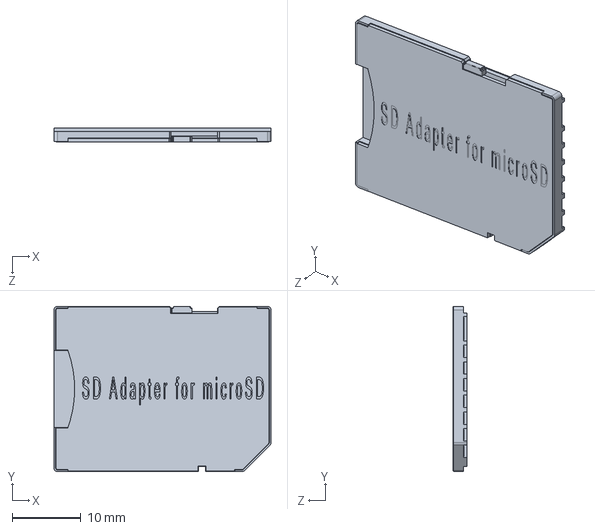
[picture p167: CAD file, 2017-11-03]
SolidWorks/P4/P4_SD_Adapter.SLDPRT
31.5 x 24.0 x 2.06 mm
