glydrfreak/vSpeed-Vario/SolidWorks/P4/P4_MICRO_SD_BREAKOUT.SLDPRT

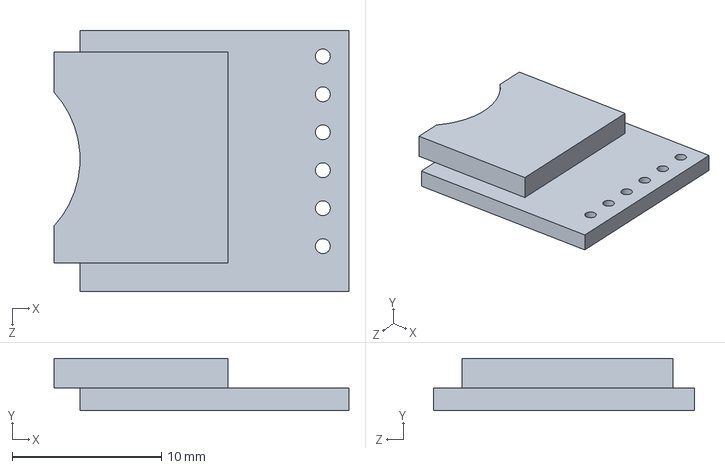
[picture p168: CAD file, 2017-11-03]
SolidWorks/P4/P4_MICRO_SD_BREAKOUT.SLDPRT
19.7 x 3.50 x 17.5 mm
