glydrfreak/vSpeed-Vario/SolidWorks/P4.new/CARABINER SUP AIR.SLDASM

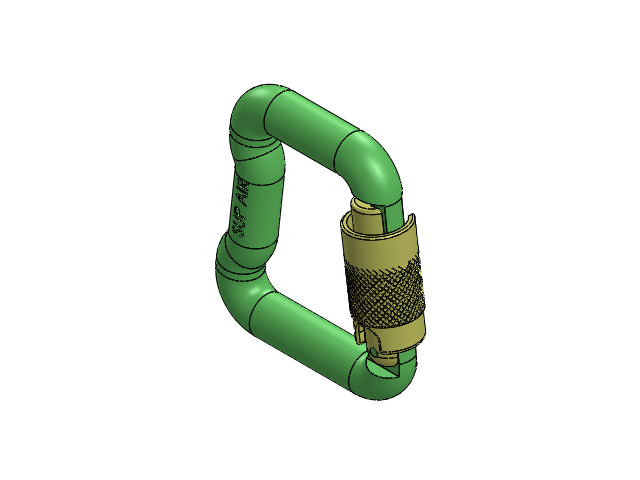
[picture p169: CAD file, 2018-03-09]
SolidWorks/P4.new/CARABINER SUP AIR.SLDASM
CARABINER_MAIN
CARABINER_ARM
CARABINER_LOCK
