glydrfreak/vSpeed-Vario/Android/vSpeedVario/app/src/main/java/com/braedin/butler/vspeed/vario/app/settings/PreferencesFragment.java

package com.braedin.butler.vspeed.vario.app.settings;


import android.content.Context;
import android.content.SharedPreferences;
import android.os.Bundle;
import android.preference.EditTextPreference;
import android.preference.ListPreference;
import android.preference.MultiSelectListPreference;
import android.preference.Preference;
import android.preference.PreferenceCategory;
import android.preference.PreferenceFragment;
import android.preference.PreferenceGroup;
import android.preference.PreferenceManager;
import android.util.Log;

import com.braedin.butler.vspeed.vario.BuildConfig;
import com.braedin.butler.vspeed.vario.R;
//import com.adafruit.bluefruit.le.connect.app.UartActivity;
import com.braedin.butler.vspeed.vario.app.vSpeedVarioActivity;
import com.braedin.butler.vspeed.vario.app.update.FirmwareUpdater;


public class PreferencesFragment extends PreferenceFragment implements SharedPreferences.OnSharedPreferenceChangeListener {
    // Log
    private final static String TAG = PreferenceFragment.class.getSimpleName();

    @Override
    public void onCreate(Bundle savedInstanceState) {
        super.onCreate(savedInstanceState);

        // Load the preferences from an XML resource
        addPreferencesFromResource(R.xml.preferences);
        initSummary(getPreferenceScreen());

        PreferenceManager.setDefaultValues(getActivity(), R.xml.preferences, false);
        setupSpecialPreferences();
    }

    @Override
    public void onResume() {
        super.onResume();
        // Set up a listener whenever a key changes
        getPreferenceScreen().getSharedPreferences().registerOnSharedPreferenceChangeListener(this);
    }

    @Override
    public void onSharedPreferenceChanged(SharedPreferences sharedPreferences, String key) {
        Log.d(TAG, "Pref changed: " + key);
        updatePrefSummary(findPreference(key));
    }

    private void setupSpecialPreferences() {
        SharedPreferences sharedPreferences = PreferenceManager.getDefaultSharedPreferences(getActivity());

        // Update summaries
        updateEditTextPreferenceSummary("pref_uarttextmaxpackets");
        updateEditTextPreferenceSummary("pref_updateserver");

        // Set ignored version
        {
            String ignoredVersion = sharedPreferences.getString("pref_ignoredversion", null);
            EditTextPreference etp = (EditTextPreference) findPreference("pref_ignoredversion");
            etp.setSummary(ignoredVersion);
            etp.setText(ignoredVersion);
        }

        // Set reset button
        Preference button = findPreference("pref_reset");
        button.setOnPreferenceClickListener(new Preference.OnPreferenceClickListener() {
            @Override
            public boolean onPreferenceClick(Preference arg0) {
                Log.d(TAG, "Reset preferences");

                // Reset prefs
                SharedPreferences preferences = PreferenceManager.getDefaultSharedPreferences(getActivity());
//                PreferenceManager.setDefaultValues(getActivity(), R.xml.preferences, true);
                SharedPreferences.Editor editor = preferences.edit();
                editor.clear();
                editor.apply();

                // Refresh view
                setPreferenceScreen(null);
                addPreferencesFromResource(R.xml.preferences);

                // Setup prefs
                setupSpecialPreferences();

                return true;
            }
        });

        // Hide advanced options (if not debug)
        if (!BuildConfig.DEBUG) {
            PreferenceCategory category = (PreferenceCategory) findPreference("pref_key_update_settings");
            Preference updateServerPreference = findPreference("pref_updateserver");
            category.removePreference(updateServerPreference);

            Preference versionCheckPreference = findPreference("pref_updatesversioncheck");
            category.removePreference(versionCheckPreference);
        }
    }

    private void initSummary(Preference p) {
        if (p instanceof PreferenceGroup) {
            PreferenceGroup pGrp = (PreferenceGroup) p;
            for (int i = 0; i < pGrp.getPreferenceCount(); i++) {
                initSummary(pGrp.getPreference(i));
            }
        } else {
            updatePrefSummary(p);
        }
    }

    private void updatePrefSummary(Preference p) {
        if (p instanceof ListPreference) {
            ListPreference listPref = (ListPreference) p;
            p.setSummary(listPref.getEntry());
        } else if (p instanceof EditTextPreference) {
            updateEditTextPreferenceSummary(p.getKey());
        } else if (p instanceof MultiSelectListPreference) {
            EditTextPreference editTextPref = (EditTextPreference) p;
            p.setSummary(editTextPref.getText());
        }
    }

    private void updateEditTextPreferenceSummary(String key)
    {
        SharedPreferences sharedPreferences = PreferenceManager.getDefaultSharedPreferences(getActivity());

        if (key.equals("pref_uarttextmaxpackets"))
        {
            // Set pref_uarttextmaxpackets
            final int uartTextMaxPackets = getUartTextMaxPackets(getActivity());

            EditTextPreference etp = (EditTextPreference) findPreference("pref_uarttextmaxpackets");
            String summary = String.format(getString(R.string.settings_uarttextmaxpackets_summary_format), uartTextMaxPackets);
            etp.setSummary(summary);
            etp.setText("" + uartTextMaxPackets);
        }
        else if (key.equals("pref_updateserver"))
        {
            // Set updateserver
            String updateServer = sharedPreferences.getString("pref_updateserver", FirmwareUpdater.kDefaultUpdateServerUrl);
            EditTextPreference etp = (EditTextPreference) findPreference("pref_updateserver");
            etp.setSummary(updateServer);
            etp.setText(updateServer);
        }
    }

    public static int getUartTextMaxPackets(Context context) {
        SharedPreferences sharedPreferences = PreferenceManager.getDefaultSharedPreferences(context);
        String uartTextMaxPacketsString = sharedPreferences.getString("pref_uarttextmaxpackets", "" + vSpeedVarioActivity.kDefaultMaxPacketsToPaintAsText);

        // Extract integer (and check for exceptions)
        int uartTextMaxPackets = vSpeedVarioActivity.kDefaultMaxPacketsToPaintAsText;
        try {
            uartTextMaxPackets = Integer.parseInt(uartTextMaxPacketsString);
        } catch (NumberFormatException ignored) {
        }
        if (uartTextMaxPackets<1) uartTextMaxPackets = 1;       // Mininum value is 1

        return uartTextMaxPackets;
    }
}
