glydrfreak/vSpeed-Vario/Documentation/vSpeed-mini-eBay/IMG-5797.JPG

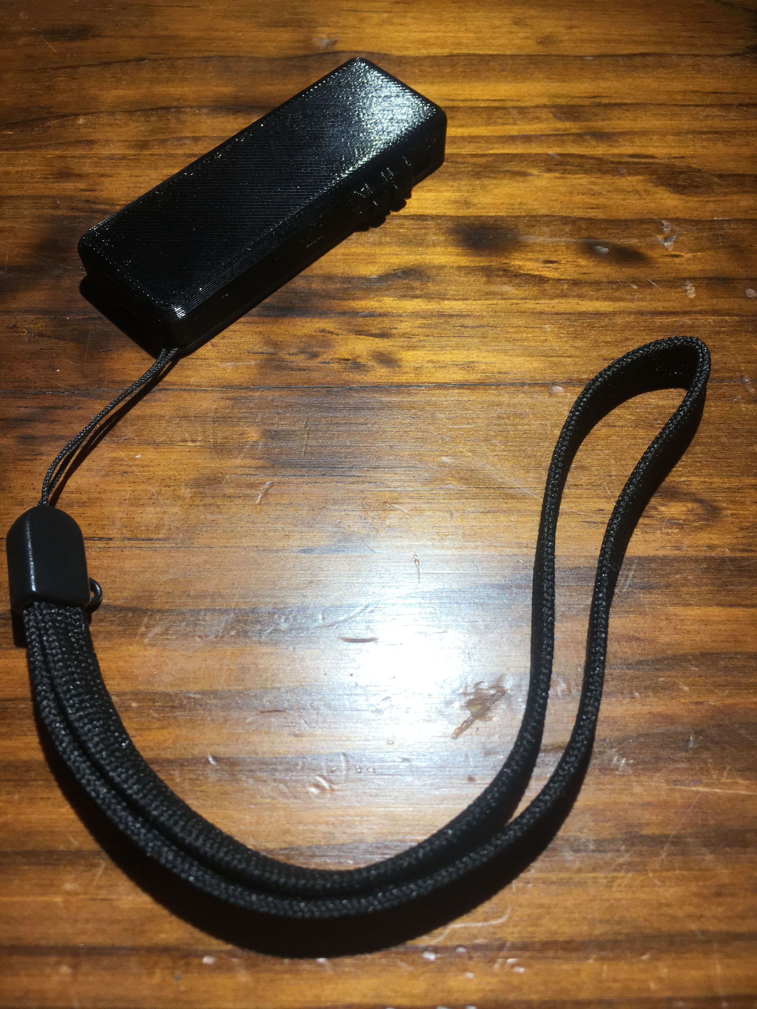
Documentation/vSpeed-mini-eBay/IMG-5797.JPG
